Skidlz/PAiA-8700/Tape Programs/Micro-Drums/Micro Drums P1 & 2.pdf

# PracticalCircuitry

# MICRO DRUMS

# PARTI

# figure2 By: Tom Henry

Analog design has always fascinated me, and as a consequence I've never really gotten into digital or computer type circuits. However, just recently I dipped into this field and was amazed at the things that even a novice (like myself) can get a computer to do. As my first venture into this area, I came up with a computer controlled drum unit, called "Micro-Drums", which has absolutely revolutionized the manner in which I approach composition. Not being a drummer, my music has always been hampered by a lack of rhythmic expression, but this new circuit has changed all that.
What is Micro-Drums? Quite simply, it is a hardware/software combination which causes the PAIA 8700 microcomputer to think that it's a drummer. Up to eight drums can1 be polytonically controlled, over the range of an entire song. Nuances, bridges, breaks, lead-ins, even mistakes can be programmed into it so that the unit really drums as if it were a person. Depending on various factors, three to ten minute songs can be programmed with a great amount of depth and variation.
Editing a drum score is quite easy since an hierarchical approach is taken which closely approximates the manner in which you would write a song anyway. Once a score has been worked out, it can be saved to cassette and re-loaded at a later date. Thus, it is possible to create a library of drum scores and this eases the task of creating new songs later on.
But here's the real kicker. By using a special technique with the computer (the IRQ, to be discussed later), we can sync the drum unit to click tracks on tape, other rhythm generators, sequencers — or we can go the other way around! That is, Micro-Drums can be either a master or slave with equal ease. And best of all, this special technique drastically reduces both the hardware and software needed.
As mentioned, this project is based on the PAIA 8700 microcomputer. However, the same methods will work with just about any other computer using a member of the 6500 family, including the VIC-20,
Commodore 64, and PET. | As long as you can find one
32 | PUtyphuny | August 1983

uncommitted address and can get access to the IRQ pin of the CPU chip, you can make it work. By the way, if you do configure this around the 8700 you'll be glad to know that the new hardware in no way interferes with the rest of the computer. You can still use it for your other applications.
Like most computer projects, the basic principle is simple although the explanations get quite long-winded. To keep things orderly, this installment of "Practical Circuitry" details the hardware needed for Micro-Drums, while next time the necessary software and programming instructions are described.
Refer to the schematic in figure 1. Essentially, we set up one address in the 8700's operating system to act as a drum output port. This port is memory mapped, and each bit in it controls a sepa-
rate drum. | Writing a byte into this port triggers
the drums corresponding to the various bits. | Ad-
dress $0880 ("$" means that the number is in hexadecimal notation) is chosen for the drum output port, since this leaves the one at $0840 free for other synthesizer applications.
IC1 and IC2 are quad latches; their duty is to store the byte which is written to the drum port. Since a typical "write" operation on the data bus is only several microseconds long, we need these two chips to grab the desired byte and hold on to it. When a "write" occurs, the STROBE line of the 8700 goes low for a microsecond or two. This line goes to pin 5 of each of the latches, hence causing them to latch the bytes currently on the data bus.

# figure 1

NOTES

MICRO-DRUMS Computer Drum Interface Designer: Thomas Henry

All resistors in ohms.
All capacitors in mfd. except where noted.
All NOR gates =1/4 4001 | (IC4, ICS).
All inverters = 1/6 4049 | (IC6).
IC POWER CONNECTIONS:
4001 --- pin 7 = ground
pin 14 -- +5V
4049 -- | pin 1 | = +5V
pin 8 | = ground
Polyphony | August 1983 | 33

# PracticalCircuitry |

But the STROBE signal also goes to 103, which is a 555 timer set up as a one-shot. The output of this one-shot, upon being fired, goes high for a period of 1 millisecond. In effect, we have stretched out the STROBE signal (which is several microseconds long) to a 1 millisecond pulse. You will recognize this figure as being one of the standards we've talked about previously — it’s just the right length of time to fire envelope generators and drum circuits. In point of fact, every output in Micro-Drums generates a +5V, 1 millisecond wide pulse, and thus the circuit is compatible with any of the projects described in "Practical Circuitry".
By the way, notice how everything works out conveniently for the 555 input at pin 2. Normally, you have to provide some input conditioning to this pin, but as it turns out the STROBE signal from the 8700 has the correct polarity and pulse width so that all you have to do is just hook it up directly to pin 2. That ought to refute Murphy's Law!
Now backtrack just a bit to the latch outputs. Each output is buffered by a transistor (QI through Q8, one for each bit). Note that the transistor inverts the bit; however, the NOR gate following the transistor inverts the bit again. The net effect is that the bit passes to jacks JI through J8 exactly as it was written to the drum port. To put it another way, write the number $FF to the drum port and all of the drums will be fired; write a number $00 to the port, and none of them will be fired. Note that LEDs DI through D8 turn on according to the number written to the port. These provide an excellent indication of what's going on while you're composing a song.
So, the latched data is sent to the transistors and then to the NOR gates. Now one input of each NOR gate is tied to the stretched out STROBE signal (from IC3 and the inverter). This causes the selected NOR gate to go high for a period of 1 millisecond, and as mentioned above, this is just what envelope generators and drum circuits like to see. Notice that the stretched out STROBE signal is also available at J9. This signal may be used as a SYNC output and can lock sequencers, rhythm generators, and other computers to the main timing logic. Its pulse width is also 1 millisecond.
This takes care of the drum output support hardware. As you can tell, there really isn't very much to it, and in fact it is quite similar to the other output port at $0840 on the 8700. The rest of the circuitry in figure 1 has nothing to do with the drum output, but instead provides the necessary housekeeping circuitry to round out the complete system.
Let's look at the peripheral circuitry.___ Since we will be syncing the computer through its IRQ line (interrupt request), we must condition this input
somewhat. | J10 gives us access to this line. | Cl,
R20, and the inverter form a half-monostable and as such take an input pulse of variable length and transform it into a precise 10 microsecond trigger. This trigger couples to the computer via IRQ, found at J7 on the 8700.
Why should this be a 10 microsecond pulse? The answer to this lies in the nature of the IRQ line in general. When the IRQ line of the 6503 CPU is brought low, the computer will cease whatever it is doing and jump to the service routine pointed at by the vector in location $0FFE and $0FFF. Control is then sent to this service routine, and the instructions found there will be executed until an RTI (return) command is encountered. Control is then sent back to the main program.
Now suppose that the IRQ signal which caused all of this to happen is still low. (In other words, the execution time of the service routine was shorter than the pulse width of the IRQ signal.)
What will happen? | Just what you would expect; the
routine is called again! | The upshot is that one IRQ
signal caused the service routine to be called
twice. | We clearly don't need that, so the IRQ pulse
is shaved down to 10 microseconds. | With the 8700,
10 microseconds corresponds to about 5 program instructions, so as long as the service routine is more than 5 instructions long, all will work well. Incidentally, it should be clear that the IRQ pin responds to "levels", not "edges".
As you will see next time, when we discuss the software aspects of Micro-Drums, this IRQ business is the key to the entire system. Not only does it make master/slave relationships possible, but it also allows, use to achieve a remarkable analog to digital conversion for the price of a patch cord! And as mentioned before, both the hardware and software can be drastically simplified.
The remaining three inverters of the 4049 package are put to use as a variable clock. There's nothing clever here since this circuit has been around for years. But one interesting aspect is that C4, R19 and an inverter are set up as another
half-monostable. | This time the pulse width is made
to be millisecond wide (our old standard). | R23 sets
the clock rate, and with this control the output frequency can be continuously adjusted. Even though the frequency can be changed the pulse width will remain fixed at 1 millisecond.
Just to give you a sneak preview, a patch cord will be used to connect the CLOCK OUTPUT (Jll) to the SYNC INPUT (J10), and thus interrupts can be made to occur at an adjustable frequency. This method will be employed to set the tempo of the

This just about covers the hardware aspects of Micro-Drums, but perhaps a few words about construction methods should be said. I built this circuit on a prototype circuit board (from Radio Shack), using ordinary hookup wire. If you employ this method, be sure to ponder the layout so that you won't run out of room at a crucial moment! Watch your power supply connections, but since the circuit only uses a +5V supply, this shouldn't provide any great problem. Also (need I say it?), use sockets, since this project employs CMOS integrated circuits which can be damaged by static electricity. Figure two shows the complete parts list for Micro-Drums. After constructing the circuit, give a great deal of thought on how you will interface it with the computer. I used ribbon cable and headers to complete the connections to JI and J7 on the 8700. After making the connections I mounted the board to the back of the 8700 computer itself. If you already have this computer, then you will know that it is a double-decked circuit board arrangement. By adding the Micro-Drums card, you will be left with a triple-decked affair.
And now is as good a time as any to mention a modification to the 8700 that you really ought to
34 | Polyphony | August 1983

PracticalCircuitry........

think about. I found that with just the dare-bones computer (no Micro-Drums added on), the power supply ran extremely hot. I took some measurements and discovered that the unit was drawing almost 900 mA! This is clearly way too much for the 7805 regulator to handle with such a small heatsink. The culprit, of course, is the RAM — each chip consumes almost
70 mA. | Multiply that by 8 (the number of 2112s in
the 8700), | and you've got quite a load for the
regulator to handle.
In general I like to have at least a 2:1 margin of safety, so I decided to modify the computer
accordingly. | I simply built another +5V power sup-
ply and put the RAM on their own circuit. | It's a
crazy scheme, I know, but it does work and both power supplies now run considerably cooler. What's more, in the future I will be able to add on extra circuitry since I have a little more juice to play with now.
If what I've said doesn't make any sense to you, then don't perform the modification!!! Your 8700 is a valuable instrument and you won't want to wreck it. On the other hand, if you understand about power supplies, decoupling, and computers — and if you have a steady hand for cutting PC board traces — you might want to give this a try. Remember, the RAMs must be completely on their own circuit; it's no good just wiring two power supplies in parallel (unless you get off on rampant destruction of valuable equipment and enjoy fireworks).
After building the Micro-Drums card and performing the modification (if this applies to you), you can then put the thing in a suitable house,
figure 2 shows how I did it. | This is a home-
made wooden box with two sheets of steel for a top and bottom. The 8700 is bolted to the top panel, and the keyboard shines through a square hole cut in
the metal. | I put some foam rubber around the hole
and this keeps dust and moisture out. | By the way,
the fuse, switch, and line cord are on their own small panel mounted on the back surface of the box. If you are using the PAIA 8700 power supply, then bring out the 60 Hz signal output to a front
panel jack as well. | (This is a logic level signal,
NOT the line voltage!!!) | Since this is a reliable
frequency source, it might come in handy for future

As you examine the photo fig. 2 you will probably notice some features not described in the article
(knobs, connectors, etc.). | These have nothing to do
with the Micro-Drums interface. | For example, there
are two D-25 jacks on the right side; one of these is a dummy (for future expansion) and the other is an interface to my keyboard synthesizer. When you build your unit, you might like to plan for the future, too, and leave some extra room for more '.onnectors and whatnot.
Well, that wraps up the Micro-Drums hardware and it's a good thing too, since we're out of space. But come back next time for the concluding episode and see how to implement the software for a complete
drum computer. | Until then, here's a challenge for
you to ponder: | how would you create a real time
clock using the SYNC input, the 60 Hz output, a patch cord, and a bit of software?

re-view continued from page 9

front-to-rear as well as left-toright. This 3-dimensiona1ity makes his heavily-produced electronic pop tunes a listening experience which goes beyond their significance as pop tunes. Other influences might be Zappa and Godley/Creme.

Berlin | Pleasure Victim | (Geffen
2036). | I didn't want to like this
group — their music is too trendy and their videos have been a little pretentious. But after having played the record numerous times looking for a weakness to attack, I have to admit it grew on me; Terri Nunn's voice has a cloying innocence and John Crawford's and David Diamond's synthi backing is very professional. It's well defended from sharks like me.
Men at Work | Business as Usual
(Columbia FC37978); Cargo | (Colum-
bia QC38660). | MAW has been called
"the Velveeta of pop". | However,
it's | precisely because | their
strong, well-crafted tunes appeal to even a jaded old reviewer that they're selling so many records. Despite the cheese.
Deckard/Cardwell/Vosh | Sound
(cassette). | "Sound" is what it's
all about, | as this synthesizer
trio spins long, | introspective
pieces full of original synthesizer sounds. Sounds that soothe, sounds that startle, sounds that bounce off the wall and refuse to leave -- always the devotion for The Sound. $4 postpaid from David Vosh, 6300 Goldenrod Court, Upper
Marlboro, MD | 20772.
Everfriend | Key Essentials | (cas-
sette). | Keyboard artist Bill
Rhodes displays his skills, from Keith Emerson-like classical rock to piano fusion jazz to the dramatic' "I,ife and Death of a Star" (reviewed May/June '81 as an EP). There's a couple vocal numbers too — too bad the vocalist he chose sounds a little tentative. Never mind; the rest is top drawer. Contact Bill at 1 Windemere Rd., Piscataway, NJ 08854.
continued on page 44

The new Series V Digital/Analog Keyboard Controllers from PAIA offer enough standard features and options tofill every need
| from stage to studio. | Standard features
include Pitch & Modulation Wheels, Gate and Re-trigger outputs, Low Note Rule Priority, Smooth Pratt-Read Action, Light
| weight and only 2" high.
| You have your choice of:
| • 37 or 61 Note Actions • Exponential Or Linear C.V. • MIDI or Parallel Digital • Mono or Poly • Factory Assm. or Low Cost Kits

Best of all, prices start at less than $180

## call ourtoll-freeline

1-800-654-8657

| 9AM to 5PM CST MON FRI

## for price& ordering details & get yourfree RAiA catalog!

Direct mailorders and inquiries to. Dept.11y
miAElectronics, Inc.

.1020 W Wilshire . Oklahoma City. OK 73116 (405)843 9626 J

i-oiyphony | August 1983 | 35

# PracticalCircuitry

# MICRO □RUMS

# PART II

# By: Tom Henry

Last time in "Practical Circuitry" we discussed the hardware needed to implement Micro-Drums, a computer controlled drum unit. In this installment we will consider the software side of things. Since a lot needs to be said, let's jump right in and see how to punch up the program required to get Micro-Drums off and drumming!

Entering the program. Figure 1 shows the complete listing for Micro-Drums software. Since I used the PAIA 8700 computer, the code is written in 6502 assembly language. Those of you who plan to use Micro-Drums with some computer other than the PAIA unit will need to change the appropriate equates (at the start of the program) and may also need to alter the starting address. The source code in Figure 1 is heavily annotated, so you should be able to figure out how it works quite easily.
8700 users can ignore the
line numbers, labels, mnemonics and comments if desired, since all that is needed to enter the program is the start address and the required code (under the heading "CODE", in the listing). Refer to your 8700 Computer/Controller manual for help in deciphering an assembler listing if you experience any difficulty.
Follow these steps to enter the program:
(1) Turn on the computer and hit the reset button.
(2) Load location $ED with the byte $1F. This sets the stack to a known condition needed by

Micro-Drums.

(3) Get ready to start loading data at $0120, by punching in this address and hitting the DISP
(4) Using Figure | 1 | as | a
guide, start entering the data. The first few bytes are $20, $34, $0F, A5, etc.
(5) Keep entering data until you hit the last byte in the list-
ing. | This is $02 (at location
$0288). | Use the PCH and PCL keys
to confirm that you're at the right place.
(6) You're now ready to save the program to tape. Follow the normal 8700 Cassette Interface protocol for saving a program. The start address in $1020, the end address is $0288, and you can use $01 for an identifier.

If all has gone well, you now have a working copy of the Micro-Drums program. After debugging your work (if needed), make a few backup copies as well. Now, let's see how to use the complete Micro-Drums system.

Using Micro-Drums. To use
Micro-Drums, follow these instructions:
(1) Reset the 8700 computer.
(2) Load location $ED with the byte $1F. This sets the stack to a known condition needed by Micro-Drums. Do not forget this step; the program will not load or run correctly if it is left out!
(3) Using the standard load-
ing procedure, | load the Micro-
Drums software. | The start address
is $0120, the end address is $0288 and the identifier is $01.
(4) Run the program by typing $025F and hitting the RUN key. If everything has gone well, you will hear a long beep. This long beep indicates that you are in the main loop, and the computer is awaiting your instructions.

When in the main loop (as you now are), you have a choice of four commands. They are COARSE EDIT, FINE EDIT, TAPE and PLAY. After any of these commands have been executed, you will always be ushered back to the main loop. Even though the 8700 has limited display capabilities, you can always tell when you are back in the main loop by the long beep. Also, if you hit an invalid key when in the main loop, a long beep will occur. By listening for this beep, you can always tell what's happening at any moment.
Here follows a description of the four main commands. Note that when within the four main commands, there are other minor subcommands possible.

FIKE EDIT. The fine edit
command defines measures of patterns which will be used as the basis for the entire song. You may define up to eight different patterns, each one up to 32 beats long. Or you may partition this in other ways; for example, four patterns of 64 beats each.
Each pattern is given a num-
ber-name. | The numbers 0 through 7
18 | Polyphony | October 1983

are used for this purpose. To start editing a given pattern, when in the main loop type the number-name and then hit the PCL key. (Mnemonic: think of PCL as "low", for lowest level of edit-
ing, | the pattern.) | So to start
editing pattern zero, type $00 and then hit the PCL key.
You will now be sent from the main loop to the FINE EDIT routine. The display will show the current beat number, and the drum LEDs will show the drums to be played during that beat. To turn a drum on for the beat, touch one of the keys from 0 to 7. The corresponding LED will light up, and all of the currently selected drums will be played as a test. You can turn a drum off by touching the corresponding drum key again. Thus, the drum keys are like toggle switches and may be used to turn drums either on or
off. | There is one limitation,
though: | you may not have a parti-
cular beat play all eight drums at once. You can have up to seven drums playing at once, but not all of them. (The software uses the all-eight condition as an end-ofthe-pattern marker.)
When you have achieved the selection of drums desired, touch the ENTER key. This will store the selection, then increment the beat pointer. The display will show the next beat number, and you are all set to enter the next selection. Also, when the display increments, the drums currently selected for the new beat will be triggered once. Thus you can single step through a pattern, for trial purposes, just by touching the ENTER key repeatedly. You can back step with the BACK key just as easily. And if you want to hear the current beat several times, touch the DISP key. This will sound the current drum selec-
| As mentioned, | keys 0 to 7
stand for drums 0 to 7. | Key 8
stands for a rest. | This clears
out the drums selected for that beat. When you are done editing a pattern, touch the 9 key and you will be ushered back to the main loop. Note that even though the pattern may be up to 32 beats long, you are not obligated to use all of the beats. For example, with 5/4 time you might want to only use 10 beats.
| COARSE EDIT. | After creating
some patterns (see above), | you

OOOO1
00002
00003
00004
00005
00006
00007
00008
00009
OOOIO

00012
00013
00014
00015
00016
00017
00018
00019
00020
00021
00022
00023
00024
00025
00026
00027
00028
00029
00030
00031
00032
00033
00034
00036
00037
00038

OOOO
OOOO
OOOO
OOOO
OOOO
OOOO
OOOO
OOOO
OOOO
OOOO

OOOO

OOOO
OOOO
OOOO
OOOO
OOOO

OOOO
0120
0120 20 34 OF

?*<*<«»*•**«»*»***«»*•*«*****«•*********
S» | | | *
J* | MI8RO-DRUMS | *
;* | MICROCOMPUTER CONTROLLED DRUM UNIT | *
;* | | | *
S* | (8) 1983 | THOMAS HEl'tfiY | *
5* | VERSION 2.1 | FEBRUARY 5, 1983 | *

I
s
IROVES --- *OO | ; IRQ VE8T0R.
PATTER --- «O3 | J PATTERN POINTER BASE.
SELE8T = 405 | ;DRUM SELE8T BIT PATTERNS.
PARAMS --- *OD | J TAPE PARAMETERS.
BEAT | = *14 | ;CURRENT BEAT POINTER.
SPOINT -- 415 | 5CURRENT EVENT SELECTED.
REPEAT -- *16 | ; CURRENT REPEAT COUNTER.
BUFFER -- *FO | J KEYBOARD BUFFER.
SCORE | = *0280 | ;DRUM SCORE AREA.
DISPLA --- *0820 | i DISPLAY ADDRESS.
DRUMS | --- *0880 | J DRUM OUTPUT ADDRESS.
RELAYS -- *OE25 | 5 TURN ON TAPE RELAYS.
CASS | = «0EAA | ;PERFORM CASSETTE OPERATION.
DECODE -- *OFOO | 5 INPUT A BYTE.
SETKEY -- *OF1F | JGET A BYTE.
BEEP | -- *OF22 | ; BEEP THE BEEPER.
LBEEP | = *OF24 | JWITH SETUP, GIVES LONG BEEP.
SHIFT | -- *OF34 | JSHIFT BUFFER BY ONE DIGIT,

s
J»»* MAIN LOOP ***

* = *0120
S
NUMBER JSR SHIFT | JSHIFT IN NEW DIGIT.
00039 | 0123 | AS FO | | LDA BUFFER | 5FETCH PACKED ENTRY.
00040 | 0125 | 8V 20 08 | | STA DISPLA | J THEN UPDATE THE DISPLAY.
00041 | 0128 | 4C 31 01 | | JMP INPUT | ;go get next input.
00042 | 0128 | A2 FF | MAIN | LDX #*FF | SGET READY FOR LONG BEEP.
00043
00044 | O12D | 18
| O12E | 20 24 OF | | CLC
| | | | JSR LBEEP | 5 DO LONG BEEP.
00045 | 0131 | 20 IF OF | INPUT | JSR GETKEY | ;WAIT FOR KEYSTROKE.
00046 | 0134 | C9 IO | | CMP #*10 | J IS IT A NUMBER?
00047 | 0136 | 90 E8 | | BCC NUMBER | J YES, BRANCH BACK AND GET
00048 | 0138* C9 10 | FIND | CMP #«1O | JIS IT 'PLAY'?
00049
00050 | O13A | FO OF
0138 C9 14
| | | | BEQ PCMD
| | | | CMP #*14 | $IS IT ’COARSE’?
00051
00052 | O13E | FO 52
0140 C9 15
| | | | BEQ COARSE
| | | | CMP #*15 | ;IS IT 'FINE'?
00053
00054

0142 FO OA
0144 C9 16
| | | | BEQ FINE
| | | | CMP #*16 | JIS IT 'TAPE'?
00055 | 0146 | DO E3 | | BNE MAIN | 5RAN OUT OF COMMANDS.
00056 | 0148 | 4C 37 02 | | JMP TAPE
00057 | 0148 | 4C E3 O1 | PCMD | JMP PLAY
00058
00059
00060
00061
00062
00063 | 014E
| 014E
| 014E
| O14E
| 014E | A5 FO | r
;»*» FINE EDIT COMMAND *»•
| | | S
| | | FINE | LDA BUFFER | J GET PATTERN NUMBER.
00064 | 0150 | 20 57 02 | | JSR OFFSET | J GET PATTERN OFFSET.
00065 | 0153 | AO 00 | | LDY #*OO | J ZERO OUT THE BEAT POINTER.
00966
00067
00068

0155 C8
0156 88
0157 8C 20 08

SHOWIT INY
BACKUP DEY
| | | | STY DISPLA | J DISPLAY IT.
00069 | O15A | Bl 03 | | LDA (PATTER),Y | »GET SELECTED BEAT,
00070 | 0158 | 8D 80 08 | | STA DRUMS | J AND PLAY IT.
00071 | 015F | 20 4F 02 | FEDIT | JSR FETCH | J GET EDIT KEYSTROKE.
00072 | 0162 | 89 12 | | CMP #*12 | SIS IT A ’BACK’?
00073 | 0164 | FO FO | | BEQ BACKUP | 5YES, BACKSPACE ONCE.
00074 | 0166 | 89 11 | | CMP #*11 | SIS IT A ’DISP’?
00075 | 0168 | FO EB | | BEQ SHOWIT | SYES, PLAY CURRENT BEAT.
00076 | 016A | 89 OA | | CMP #*OA | SIS IT A DRUM NUMBER (0-9)?
00077 | 0168 | 90 08 | | BCC DENTER | SYES, GO ENTER DRUM BEAT.
00078 | 016E | 89 13 | | CMP #*13 | SIS IT AN 'ENTER'?
00079 | 0170 | DO ED | | BNE FEDIT | SNO, RAN OUT OF COMMANDS.
00080
00081

0172 88
0173 48 55 O1
| | | | INY | SYES, ADVANCE TO NEXT BEAT.
| | | | JMP SHOWIT
00082 | 0176 | 89 09 | DENTER CMP #*09 | S#*09 MEANS END OF PATTERN.
00083
00084

0178 DO 06
| O17A | A9 FF | | BNE NEXT1
| | | | LDA #*FF | SEND OF PATTERN MARKER.
00085
00086

0178 91 03

| 017E | DO AB | | STA (PATTER),Y
| | | | BNE MAIN | 5 BRANCH ALWAYS.
00087 | 0180 | 89 08 | NEXT1 | CMP #*08 | J#*08 MEANS ’REST’
00088
00089
00090

0182 DO 04
0184 A9 00
0186 FO 05
| | | | BNE NEXT2
| | | | LDA #*0O
| | | | BEQ STORE | 5 BRANCH ALWAYS.
00091
00092

0188 AA
0189 B5 05
| | | NEXT2 | TAX | ;INDEX INTO BIT PATTERN.
| | | | LDA SELECT,X | SGET PROPER BIT PATTERN.
00093 | O18B | 51 03 | | EOR (PATTER),Y | 5 ADD IN NEW BEAT.
00094 | O18D | 91 03 | STORE | STA (PATTER),Y | SAND SAVE IT.
00095 | O18F | 48 55 O1 | | JMP SHOWIT | ;SOUND THE DRUM BEAT.
Pobphony | October 1983 | 19

00096 0192
00097 0192
00090 0192
00099 0192
OOIOO | 0192
OO101 | 0192 | A6 FO
00102 | 0194 | 86 15
00103 | 0196 | A6 15
00104 | 0198 | BD 80 02
00105 | 0198 | 85 FO
00106 | O19D | SO 20 08
00107 | 01 AO | 20 IF OF
00108 | O1A3 | C9 IO
00109 | O1A5 | 80 08
001 IO | 01A7 | 20 34 OF
OO111 | O1AA | A5 FO
OO112 | O1 AC | 4C 9D 01
OOl 13 | 01AF | C9 13
OO114 | 0181 | DO OC
OOl 15 | 0183 | A6 15
OOl 16 | 0185 | A5 FO
OOl 17 | 0187 | 90 80 02
OO 118 | O1BA | 15
00119 | O1BC | 4C 96 O1
00120 | O1BF | C9 12
00121 | O1C1 | DO 05
00122 | 01C3 | C6 15
00123 | 01C5 | 4C 96 01
00124 | O1C8 | C9 14
00125 | 01CA | DO 05
00126 | 01CC | A5 15
00127 | O1CE | 4C 9D O1
OOl 28 | O1D1 | C9 11
00129 | O1D3 | FO Cl
00130 | 01 D5 | C9 17
00131 | O1D7 | DO C7
OOl 32 | O1D9 | A6 15
00133 | O1DB | A9 OO
OO 134 | O1DD | 9D 80 02
00135 | OiEO | 4C 28 O1
00136 01E3
00137 O1E3
00138 O1E3
OOl 39 O1E3
00140 O1E3
00141 | 01E3 | A9 00
00142 | 01E5 | 85 16
00143 | 01E7 | A9 FF
00144 | O1E9 | 85 15
00145 | O1EB | 58
00146 | 01EC | C9 FF
OO147 | OlEE | FO FC
00140 | O1FO | 4C 28 01
00149 01F3
00150 01F3
00151 | O1F3 | 20 OO OF
00152 | 01F6 | C9 OO
00153 | 01F8 | DO 04
00154 | 01FA | 28
00155 | O1FB | 78
00156 | O1FC | 08
00157 | O1FD | 40
00158 O1FE
00159 O1FE
00160 | 01FE | A5 16
00161 | 0200 | DO 19
00162 | 0202 | E6 15
00163 | 0204 | A6 15
00164 | 0206 | BD 80 02
00165 | 0209 | FO EF
00166 | 0208 | 85 16
OO167 | O20D | E6 15
00168 | 02OF | A6 15
00169 | 0211 | BD 80 02
00170 | 0214 | 20 57 02
00171 | 0217 | A9 OO
00172 | 0219 | 85 14
OOl73 | 0218 | A4 14
00174 | 021D | Bl 03
00175 | O21F | C9 FF
00176 | 0221 | DO 08
00177 | 0223 | C6 16
00178 | 0225 | A9 00
00179 | 0227 | 85 14
00180 | 0229 | FO C8
00181 | 0228 | 8D 80 08
00182 | O22E | 8C 20 08
00183 | 0231 | E6 14
00184 | 0233 | A9 FF
00185 | 0235 | DO
00186 0237
00187 0237
00180 0237
00189 0237

1
J*»* COARSE EDIT COMMAND ***
COARSE LDX BUFFER | J GET DESIRED EVENT NUMBER.
| STX SPOINT | S STORE AT CURRENT EVENT.
REVEAL LDX SPOINT
| LDA SCORE,X | J GET CONTENTS OF EVENT.
| STA BUFFER | JPUT IN BUFFER AND
VIEW | STA DISPLA | JSHOW IT TOO.
LOOP | JSR SETKEY | 5 GET KEYSTROKE.
| CMP #♦10 | J CHECK FOR NUMBER.
| BCS NONUM | J NOT A NUMBER, BRANCH.
| JSR SHIFT | JSHIFT IN NEW DIGIT.
| LDA BUFFER | ;FETCH PACKED ENTRY.
| JMP VIEW | J AND UPDATE DISPLAY.
NONUM | CMP #$13 | ;IS IT AN ’ENTER’?
| BNE NEXT3 | J NO, GO ON.
| LDX SPOINT | J RE-GET EVENT NUMBER.
| LDA BUFFER | ;FETCH INPUT NUMBER.
| STA SCORE,X | 5 STORE IN SCORE.
| INC SPOINT | ;UPDATE EVENT NUMBER.
| JMP REVEAL | JUPDATE DISPLAY.
NEXT3 | CMP G$ 1? | JIS IT A BACKSPACE?
| BNE NEXT4 | J NO, BRANCH ON.
| DEC SPOINT | 5DECREMENT EVENT COUNTER.
| JMP REVEAL | ;SHOW CONTENTS OF EVENT.
NEXT4 | CMP #♦14 | J IS IT A ’PCH’?
| BNE NEXT5 | ;NO, BRANCH ON.
| LDA SPOINT | 1 GET CURRENT EVENT NUMBER.
| JMP VIEW | ;AND SHOW IT.
X T5 | CMP #♦11 | JIS IT A ’DISP’?
| BEQ REVEAL | J IF SO, SHOW CONTENTS.
| CMP #♦17 | J’REL’ STANDS FOR ALL DONE.
| BNE LOOP | J RAN OUT OF COMMANDS.
| LDX SPOINT | J RE-GET EVENT NUMBER.
| LDA #♦00 | J END OF SCORE MARKER.
| STA SCORE,X
j | JMP MAIN | J RETURN TO MAIN LOOP.

’LAY’ COMMAND ENTRY ***

play | LDA #♦00 | J ZERO OUT REPEAT AND
| STA REPEAT | J SCORE POINTER.
| LDA •♦FF
| STA SPOINT
| CLI | JPREPARE FOR IRQ.
TISHT | CMP •♦FF | J•♦FF MEANS KEEP PLAYING.
| BEQ TIGHT | J STAY IN TIGHT LOOP.
| JMP MAIN | J ABORT ’PLAY’ NOW.
IRQRTN JSR DECODE | J SEE IF ZERO KEY IS PUSHED.
CMP •♦OO
BNE PLAMOR | J IT ISN’T, SO PLAY MORE.
FINISH PLP | J SET INTERRUPT FLAG
SEI | J SO NO MORE OCCUR.
PHP
RETURN RTI
PLAMOR LDA REPEAT | JREPEATED OLD PATTERN ENOUGH?
BNE MORE | J NO, KEEP GOING WITH OLD ONE.
INC SPOINT | J YES, UPDATE SCORE POINTER.
LDX SPOINT
LDA SCORE,X | J GET REPEAT TIME DATA.
BEQ FINISH | J DONE PLAYING WHOLE SCORE.
STA REPEAT | J CONTAINS NUMBER OF REPEATS.
INC SPOINT | J UPDATE SCORE POINTER.
LDX SPOINT
LDA SCORE,X | J GET PATTERN NAME DATA.
JSR OFFSET | J GET PATTERN ADDRESS OFFSET.
LDA •♦OO
STA BEAT | J ZERO OUT BEAT POINTER.
MORE | LDY BEAT | JY INDEXES TO PROPER BEAT.
LDA (PATTER),Y | JGET OUTPUT DATA.
CMP •♦FF | J END OF PATTERN?
BNE OKAY | J NO, GO PLAY THE BEAT.
DEC REPEAT | J DECREMENT REPEAT TIME.
LDA #♦00 | JYES, RESET BEAT COUNTER.
STA BEAT | J THEN TRY AGAIN.
BEQ IRQRTN | (BRANCH ALWAYS.
OKAY | STA DRUMS
STY DISPLA
I | BEAT | J UPDATE BEAT POINTER.
LDA •♦FF
BNE RETURN | J BRANCH ALWAYS.

; *»* ’LOAD’ AND ’SAVE’ COMMAND *** will then string them together in various arrangements to form the
complete song. | This is COARSE
editing. | You will create a score
by entering some events; | each
event consists of two entries. The first entry is the number of times you wish a pattern to repeat , and the second entry is the number-name of the pattern which
is to be repeated. | There is room
for 64 events total. | This will
allow songs up to fifteen minutes long to be programmed! To g»t into the COARSE EDIT mode from the main loop, type the number of the event you wish to start at (usually a $00) and then the PCH key. (Mnemonic: think of PCH as "high", the highest level of editing.) The display will now show the contents of the current event. To enter a new event, type the desired number and hit the ENTER key. The event will be recorded, and the score pointer is incremented once. For example, starting at event zero, to get sixteen repeats of one, type $10, ENTER, $01, ENTER. Note that all numbers are in hexadecimal and that each entry must be followed by an EN-TER.
You can backspace through a score with the BACK key. Also, to see the current event number, touch the PCH key at any time. To see the contents of the event, type DISP. Using the keys just mentioned, you can step through an entire score in a matter of minutes and change or update it as needed.
To finish off a score, touch the REL key. This puts in an end of score marker and returns you to the main loop. A long beep will occur.
PLAY. | Playing a score is
easy. | First make sure that the
SYNC INPUT jack has some source of triggers. You may sync the drum score off of the internal variable clock, an external clock, keyboard triggers, sequencer triggers, or click tracks from a tape deck. The input pulses should be +5V in magnitude. Note that Micro-Drums' internal variable clock meets this need and is perhaps the easiest to
use. | In addition it allows easy
adjustment of the tempo: | just
dial in the desired speed. | This
may not seem like much, but consider what we've just done: a potentiometer controls the tempo, continuously, without the intervention of an analog to digital con-
20 | PObliiony | October 1983

verter. How's that for saving money and keeping things simple! After providing some source of sync pulses, you may start playing the score simply by touching the RUN key. When the song is finished, you will be sent back to the main loop and a long beep will occur. You can also abort a song while it is playing by touching the 0 key. Once again, you will return to the main loop.
As you can see, the SYNC
INPUT (alias the IRQ) is the key to the power of Micro-Drums. Any circuit which can put out a series of pulses can cause Micro-Drums to step through the song, beat after beat. You are not constrained to meet this or that condition, and the circuitry is perfectly general. Simply send the computer some pulses and the song commen-
ces! | And don't forget the SYNC
OUTPUT jack either. | You can cause
some other circuit (like a sequencer) to follow Micro-Drums just as easily, so Micro-Drums can thus play the role of master or slave with equal ease.
TAPE. | You can save or load
scores using this command. | To
save a score, start the recorder going in the record mode, type $DD and touch the TAPE key. The computer will do the rest; there is no need to enter any addresses,

Loading a score is just as easy. Start the recorder going in the play mode, type $11 and hit the TAPE key. The score will be loaded.
At the end of any tape operation you will be sent back to the main loop, and a long beep will indicate this fact. Note that the load and save options affect the entire score and pattern memory, so don't be alarmed if the operation takes up to a minute or so. If you experience any trouble, refer to the 8700 Cassette Interface manual and review how to set volume levels and so on.

The future. Well, that just about wraps up how to use Micro-Drums. Of course, all we have done here is talk about the mechanics of using the unit; it's up to you to think about the musical side of things. For example, if you know that a particular pattern is to contain both eighth notes and triplets, then you will need to divide the pattern into groups
of | twenty-four | (three | times
00190 | 0237 | | ;
OO191 | 0237 | A2 07 | TAPE | LDX #*07 | PREPARE TAPE PARAMETERS.
00192 | 0239 | 85 OC | SETFIL LDA PARAMS-1,X | ;GET PARAMETERS.
00193 | 0238 | 95 FO | | STA BUFFER,X | 5 AND STUFF IN PLACE.
00194 | 023D | CA | | DEX
00195 | O23E | DO F9 | | BNE SETFIL | ;KEEP STUFFING IF NEEDED.
00196 | 0240 | A5 FO | | LDA BUFFER | J GET LOAD/SAVE TOKEN.
00197 | 0242 | 20 25 OE | | JSR RELAYS | ;TURN ON RELAYS.
00198 | 0245 | 20 AA OE | | JSR CASS | ;PERFORM LOAD OR SAVE.
00199 | 0248 | 18 | | CLC
00200 | 0249 | 20 22 OF | | JSR BEEP | ;TURN OFF RELAYS AND BEEP.
00201 | 024C | 4C 2B O1 | | JMP MAIN | ;ALL DONE!
00202 | 024F | | 5
00203 | 024F | | ;
00204 | 024F | 84 14 | FETCH | STY BEAT | j GET A KEY, BUT SAVE
00205 | 0251 | 20 IF OF | | JSR GETKEY | ;CURRENT Y—REGISTER.
00206 | 0254 | A4 14 | | LDY BEAT
00207 | 0256 | 60 | | RTS
00208 | 0257 | | ;
00209 | 0257 | | ;
00210 | 0257 | OA | OFFSET ASL A | 5 FIND OFFSET BY
00211 | 0258 | OA | | ASL A | ;MULT IPLYING ACCUMULATOR
00212 | 0259 | OA | | ASL A | i BY SIXTEEN.
00213 | 025A | OA | | ASL A
00214 | 0258 | OA | | ASL A
00215 | 025C | 85 03 | | STA PATTER | iOFFSET ADDRESS IS HERE.
00216 | 025E | 60 | | RTS
00217 | O25F | | ;
00218 | 025F | | ;
00219 | O25F | ;*** INITIALIZATION ROUTINE **♦
00220 | O25F | | ;
00221 | O25F | | ;
00222 | O25F | 78 | | SEI
00223 | 0260 | A2 OO | | LDX #«OO
00224 | 0262 | BD 78 02 | MOVE | LDA DATA,X | ; GET DATA BYTE.
00225 | 0265 | 95 OO | | STA IRQVEC,X | 5STUFF IT INTO O-PAGE.
00226 | 0267 | E8 | | INX
00227 | 0268 | EO 14 | | CPX #*14 | ?NUMBER OF BYTES+1.
00228 | O26A | DO F6 | | BNE MOVE
00229 | O26C | AO OO | | LDY #*00 | 5CLEAR PATTERN AREA.
00230 | 026E | A9 OO | | LDA #*OO
00231 | 0270 | 91 03 | CLEAR | STA <PATTER),Y | ,
00232 | 0272 | 88 | | DEY
00233 | 0273 | DO FB | | BNE CLEAR
00234 | 0275 | 4C 28 O1 | | JMP MAIN | ,GO START UP MICRO-DRUMS.
00235 | 0278 | | ;
00236 | 0278 | | ;
00237 | 0278 | ?*»* DATA AND ADDRESS TABLES ***
00238 | 0278 | | ;
00239 | 0278 | | 5
00240 | 0278 | 4C | DATA | .BYTE *4C | ;OPCODE FOR ’JMP’.
00241 | 0279 | F3 O1 | | .WORD IRQRTN | ;START OF IRQ ROUTINE.
00242 | 027B | OO 03 | | .WORD *0300 | ;PATTERN BASE ADDRESS.
00243 | 027D | O1 | | .BYTE *01, *02 | ;DRUM SELECT BIT PATTERNS.
00243 | O27E | 02
00244 | 027F | 04 | | .BYTE *04, *08
00244 | 0280 | 08
00245 | 0281 | 10 | | .BYTE *1O, *20
00245 | 0282 | 20
00246 | 0283 | 40 | | .BYTE *40, *80
00246 | 0284 | 80
00247 | 0285 | OO | | .BYTE *OO | ;FILE PARAMETER.
00248 | 0286 | FF 03 | | .WORD *O3FF | ;TAPE END ADDRESS.
00249 | 0288 | 80 02 | | .WORD *0280 | ?TAPE START ADDRESS.
00250 | O28A | 80 02 | | .WORD *0280 | iTAPE POINTER.
00251 | 02BC | | | . END

ERRORS -- ooooo

END OF ASSEMBLY

eight). This is just one example of one of the musical considera-
tions | that must be taken into
account with Micro-Drums. | How-
ever, you will find that the more you play with Micro-Drums, the better you will become at visualizing what needs to be done.
Well, we've run out of room and need to start planning other projects. But in the meanwhile, as you play with the unit, think about how you would implement sequencer interfaces with Micro-Drums. The procedure is actually quite simple due to the "magical" way in which the SYNC INPUT works. Then consider synchro-sonic re-
cording; | how would you do this
with Micro-Drums? | Once again, the
basic principle is quite simple. Think about these things and perhaps later on in the pages of "Practical Circuitry" we can com-
pare notes. | __________________ _
Polyphony | October 1983 | 21
