Skidlz/PAiA-8700/Tape Programs/Poly-Split/Poly-Split.pdf

# POLY-SPLIT

Many times we've talked about how the personality of our computer based equipment is a function of the Operating system software that we happen to be running at the moment. Let's play some head games with the gear and feed it some code that will give it a split personality.
POLY-SPLIT does just that; it gives us two complete polyphonic synthesizer systems under the control of one keyboard. Play a chord or note on the lower keys and they are always assigned to a lower group of outputs. Play on higher keys and the result is assigned to another group.
Before we get into the listing of this program and its operation and use, we need to keep one fact clearly in mind;
POLY-SPLIT is simply an | extension | of | the | polyphonic
personality offered in MUS 1.0. All of the options offered by that code (STGs, dynamic output refresh, etc.) are provided by this one also. Since many of MUS l.O's subroutines are used by
POLY-SPLIT you must have this PROM or | its | equivalent
available, and the variables that you manually initialize for MUS 1.0 (see LAB NOTES: MUS 1.0, April/ May 1978 Polyphony) must be set for POLY-SPLIT also.
In addition to OUTS, CTRL, etc. which MUS 1.0 used there is a new variable which is unique to POLY-SPLIT; OUT2 ($BF). This is the variable that tells the program how many channels are to be set aside for use exclusively by AGO keys below the split point. Notice specifically that if MUS l.O's STG option is selected, the number entered into this variable must include those channels which will be producing envelope transients, (i.e. The number entered for OUT2 will always be an even number when STGs are being used.)
For example, if you have hardware (QuASH, etc,) for eight channels, this number is entered into the normal MUS 1.0 location for it; OUTS ($EA). If you want to split these into· three channels for low keys and five for high keys, you would set OUT2 ($BF) to contain 03.
The program appears at the end of this column and is loaded starting at location $000 in the same way that we've loaded programs in the past. If you're the careful sort, you will also save the program on tape as soon as it's loaded so that if there's a problem it won't wipe out all of your work. When the program has been loaded, preset the MUS 1.0 variables according to your preferences and application, and set the low channels variable (OUT2) as discussed above.
Run the program from location $000. With POLY-SPLIT running, keys 0 and 1 on the command keyboard retain the functions that they had under MUS 1.0. Key 0 clears and mutes the system; key 1 causes all of the channels to produce a note corresponding to middle C on the AGO keyboard.
A use for command key 2 has now been added; it provides a means of changing the split point while you're playing. Touch this pad and, as long as it's held down, any key on the AGO keyboard that you press will become the new split point. Now while playing, any key below the split point will be assigned to the channels that you've set aside for them, while keys greater or equal to the split point will be assigned to the remaining channels.

10011-
1002-
1004-
1006-
1008-
1011A-101l8-
100D-1010-
1013-
1016-
1018-
101A-101C-101E-1021-
1023-
1025-
1027-
1029-
1026-
102()-

0020

0010 :-·---

0030
8049
0050
0060
0070
0080
0090
0100 :•
:• | • :• | POLY-SPLIT | * :• | • :• A PROGRM FOR POL YPHCllIC •
:• | SPLIT KEY800IID | • :• | • :• | BY
:• | JO!tl Sil'IOOTOO | •

0110 : • <C> 1979 - PAIA ELECTROOICS * 0120 :•
0130 : ************ 1 1 1 1 1 1 1 1 1 1 • •********

0010 KTBI. • OL 00E0
0028 NTBL . OL 0008
0030 HKEY . Dl 00A2
0040 SPl T . Dl 00111
0050 ruT2 . OL 00EC
0860 oun . DL 00EB
0070 MS . Dl 00EA
0080 TRr.N . Dl OOC3
0090 !NI T . Dl 0021
0100 NOTE . Dl 0028
0110 POLY . Dl 0071
0128 DECO . OL 0F00
0130
0140 :FIRST, SYSTEM THINGS ARE DISPOSED OF. TIE SYSTEl1 IS 0150 : INITifl.IZED USING 111.JS 1. 0'S 'INIT" ROOTINE. TIEN THE 0160 : QlJASH CHANIELS ARE REFRESHED ANO TIE ffiO KE'IBOORD
0170 :SCAlfED ~ USING ROOTINES FRllf'I MUS 1 9
0180 : Fltfll.LY, THE PIEBUG ROOTINE 'DECOOE' IS USED TO READ TIE 0199 : COl'l'Rll KEYBOARD AN> ANY COl'lfH)5 ARE EXECUTED.
0280 :0-Sl'STEl1 CLEAR fW RE-INITi 1-TlM ALL ClfflNELS;
0219 :2-SET SPLIT POINT, ANY AGO KEY PRESSED BECmES SPLIT 9220
0239 . OR 1009
0240
A5 E8 | 0250 STAR LDR *OUTT | : GET THE 1 OF RESER\IED LON CtflNS
85 EC | 0260 | STA .OUT2 | : SAYE PERl'IANENTL Y
A2 97 | 0270 POSP LDX 97 | : SET UP A POINTER/CllJNTER
A9 911 | 0280 SLP9 LDR 911 | : ANO GET READY TO ZERO STUFF
95 A2 | 0290 | STA *HKEY, X : ZERO THE TEl1PORARY BUFFER
CA | 0300 | DEX | :AND POINT TO THE NEXT
10 F9 | 0310 | BPL SLP9 | : IF SOl'IE ARE LEFT, LOOP
20 21 0D 0320 | JSR INIT | : 111.JS 1. 0 - INTIFLIZE SYSTEl1
29 28 0D 0330 SLP6 JSR l«lTE | : i'JJS 1. 0 - REFRESH AND READ POO KBD
20 09 0F 0340 | JSR DECO | :PIEBlXl - REFC> COl11AND KEYBOARD
F9 EC | 0350 | 8EQ POSP | : IF Cllf'll!Atl) = 9, BRAll:H TO RE-INIT
C9 01 | 0360 | CMP 91 | : 15 COl1lfttl) = 1?
D0 97 | 0370 | BNE NTST | : l«J, BRANCH TO rEXT TEST
A9 2E | 0380 | LDA 2E | : WILL BECOME 11100LE C
20 23 0D 0390 | JSR INIT+02 : USE PART OF MUS 1 9 INITIALIZE
F0 ED | 0409 | BEQ SLP6 | : BRIKH fl.lllYS
C9 02 | 0410 NTST Cl1P 02 | : 15 COl1llAND = 2? | ----...._"
D0 08 | 0420 | BNE SPLI | : NO, BRANCH TO POL Y-SPLIT PROGRAl't
A5 E7 | 0430 | LDA *KTBL +97 : GET THE LOWEST KEY DWli
F9 E5 | 0440 | BEQ SLP6 | : IF NONE ARE DOWN, LOOP
85 R1 | 0450 | STA •SPLT | :SAYE TIE KEY AS THE SPLIT POINT
00 Ei | 0460 | illE SLP6 | : BRffDI 11..lll\'IS

67

## 1280 ********************************* 1290 :~ UOTE5:

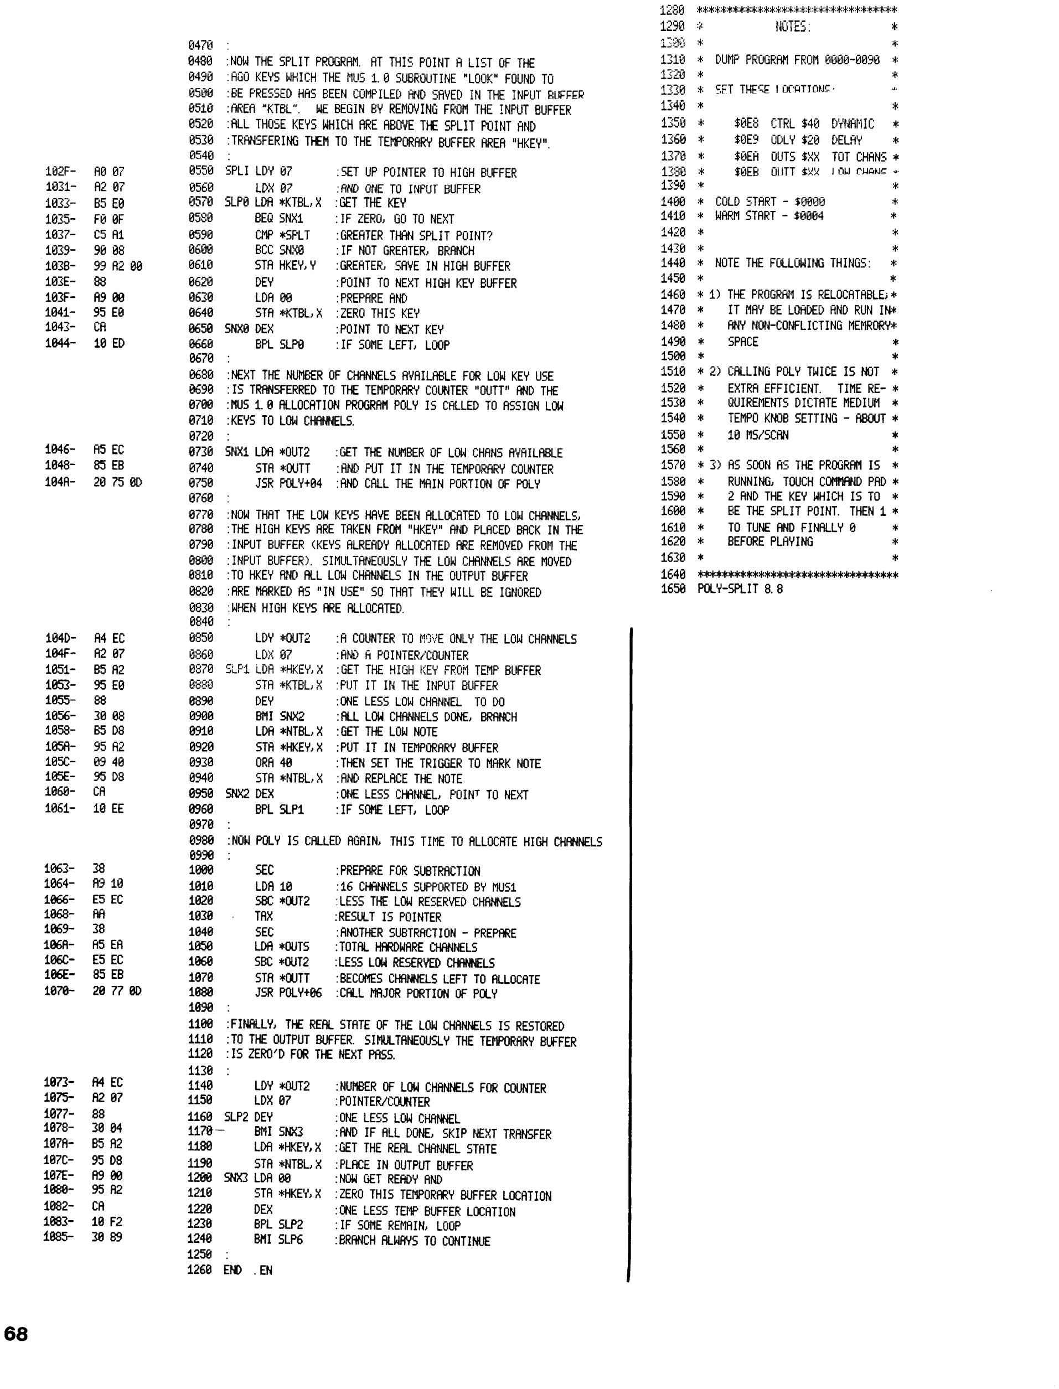
[picture p18: page 2]

0470 | 1:0ü *
0480 : NOW THE SPLIT PROGRAM. AT THIS POHff A LIST OF THE | 1310 * DUMP PROGRAM FROM 0000-0090 * 0490 : AGO KEYS WHICH THE MUS 1. 0 SUBROUTINE "LOOK" FOUND TO | E20 * 0500 : BE PRESSED HAS BEEN COMP 1 LE[l AND SAVED IN THE INPUT BllFl'E:R | rno * SFT THt='C::~ 1 ül'ATH'i,Jb ·
0510 : AREfl "KTBL ". WE BEG IN BY REMOV ING FROM THE ! NPUT BUFFER | 1340 * | * 0520 : ALL THOSE KE'rS WHICH ARE ABOVE TfE SPLIT POINT AND | 1350 * $0E8 CTRL $40 [>'rNAMIC •
0530 : TRANSFERING TfEM TO THE TEMPORARY BUFFER AREA "HKEY". | 1360 • $0E9 ODLY $20 DEUW | • 0540 | 1370 * $0EA OUTS $XX TOT CHANS •
102F- A0 07 | 0550 SPLI LD'r 07 | : SET UP POINTER TO HIGH BlffER | 1380 • t0EB Ol lTT :t~~ | J OLi C'J..JA)J~ ~·
1031- A2 07 | 0560 | LDX 0? | : AND ONE TO 1 NPUT SUFF ER | B90 *
1033- 85 EO | 0570 SLP0 LDA •KTBL, X :GET THE KEY | 1400 • COLD START - $'1000
1035- F0 0F | 0580 | BEQ SNX1 | : IF ZERO, GO TO NEXT | 1410 * WARM START - $0004
1037- | C5 Ai | 0590 | Cl1P *SPLT | : GREATER THAN SPLIT POHff? | 1420 *
1039- 90 08 | 0600 | BCC SNX0 | : IF NOT GREATER, BRANCH | 1430 * 1038- 99 A2 00 | 0610 | STA HKEY, Y : GREATER, SAVE IN HIGH BUFFER | 1440 * NOTE THE FOLLOWING THINGS: | *
103E- 88 | 0620 | DEY | : POINT TO HEXT HIGH KEY BUFFER | 1450 * | •
103F- A9 00 | 0630 | LDA 00 | : PREPARE AND | 1460 * 1l THE PROGRAM 1 S RELOCATA8LE; *
1041- 95 E0 | 0640 | STA •KTBL, X : ZERO THIS KE'r | 1470 • IT MAY BE LOADED AND RUl·I JN.•
1043- CA | 0650 SNX0 DEX | :POINT TO HEXT KEY | 1480 * ANY NOIHONFLICTING 11El1RORY*
1044- 10 ED | 0660 | BPL SLP0 | : IF SOME LEFT, LOOP | 1490 • SPACE | * 0670 | 1500 • | *
0680 : NEXT THE NUMb'ER OF CHANNELS AVAILABLE FOR LOW KEY USE | 1510 * 2) CillLING POLY TWICE 15 NOT •
0690 : 15 TRANSFERRED TO THE TEMPORARY COUNTER "OUTT" AND THE | 1520 * EXTRA EFFICIENT. TIME RE- *
0700 :MUS 1. 0 ALLOCATIOll PROGRAM POLY 15 CALLED TO ASSIGN LOW | 1530 * QUIREMENTS DICTATE MEDIUM *
0710 : KEYS TO LOW CHANNELS. | 1540 * TEMPO KNOB SETTING - ABOUT *
0720 | 1550 • 10 MSISCAN
1046- A5 EC | 0730 SNX1 LDA •OUT2 | :GET THE NUMBER OF LOW CHANS AVAILABLE | 1560 • | * 1048- 85 EB | 0740 | STA •OUTT | : AND PUT IT IN THE TEMPORARY COUNTER | 1570 * 3) AS SOON AS THE PROGRAM 15 * 104A- 20 75 0D | 0750 | JSR POL'r+04 :ANO CALL THE MAIN PORTION OF POLY | 1580 | RUNNJNG, TOUCH COMMAND PAD *
0760 | 1590 | 2 AND THE KEY WHICH 15 TO *
0770 : NOW THAT THE LOW KE'IS HAVE BErn ALLOCATED TO LOW CHANNELS, | 1600 | BE THE SPLIT POINT. THEN 1 *
0780 :THE HIGH KEYS ARE TAKEN FROM "HKE~"' AND PLACED BACK IN THE | 1610 | TO TUNE AND FINALL Y 0
0790 : INPUT BUFFER (KEYS ALREAD'r ALLOCATED ARE REMOVED FROM THE | 1620 | BEFORE PLAVING
0800 : INPUT BUFFER). SIMULTANEOUSL'I THE LOW CHANNELS ARE MOVED | 1630 * | * 0810 : TO HKE'I ANO ALL LOW CHANNELS IN THE OUTPUT BUFFER | 1640 ********************************* 0820 :ARE MfiRKED AS "IN USE" 50 THAT THE'r WILL BE IGNORED | 1650 POLY-SPLIT 8. 8

0830 WHEN HIGH KEYS ARE ALLOCATED.
0840
1040- A4 EC | 0850 | LDY •OUT2 | : A COUNTER TO M'WE ONL Y THE LOW CHANNELS
104F- A2 07 | 0860 | L[>i< 07 | : ANü fi POHITER/COUNTER
1051- 85 A2 | 0870 SLP1 LDA •HKEY, X : GET THE HIGH KEY FROM TEMP BUFFER
1053- 95 E0 | 0880 | STA •KTBL, X : PUT IT IN THE ltlPUT BLIFFER
1055- 88 | 0890 | DEY | : ONE LESS LOW CHANNEL TO DO
1056- 30 08 | 0900 | BMI SNX2 | : ALL LOW CHANNELS DONE, BRANCH
1058- 85 08 | 0910 | LDA •NTBLX : GET THE LOW NOTE
105A- 95 A2 | 0920 | STA •HKEY, X : PUT IT IN TEMPORARY BUFFER
105C- 09 40 | 0930 | ORA 40 | : THEN SET THE TRIGGER TO Mf!RK NOTE
105E- 95 DS | 0940 | STA •tHBLX : ANO REPLACE THE NOTE
1060- CA | 0950 SNX2 DEX | : ONE LESS C~NNEL, PO !NT TO NEXT
1061- 10 EE | 0960 | BPL SLP1 | : JF SOl'IE LEFT, LOOP
0970
0980 : NOW POLY 15 CALLED AGA IN, THIS TIME TO ALLOCATE HIGH CHANNELS 0990
1063- 38 | 1000 | SEC | : PREPARE FOR SUBTRACTI ON
1064- A9 10 | 1010 | LDA 10 | : 16 CHflNNELS SUPPORTED BY MUS1
1066- ES EC | 1020 | SBC *OUT2 | · LESS THE LOW RE~.ERl/ED CHANNELS
1068- AA | 1030 | TAX | : RESUL T 15 POINTER
1069- 38 | 1040 | SEC | : AMJTHER SUBTRACTION - PREPARE
106A- A5 EA | 1050 | LOA •OUTS | : TOTAL HARDWARE CHANNELS
106C- E5 EC | 1060 | SBC •OIJT2 | : LESS LOW RESERl/EO CHANNELS
106E- 85 EB | 1070 | STA *OOTT | : 8ECOl'IES CHANNELS LEFT TO ALLOCATE
1070- 20 77 0D | 1080 | JSR POLY+06 :CfU MAJOR PORTION OF PCX.Y
1090
1100 : FINALLY, TfE REAL STATE OF THE LOW CHANNELS 15 RESTORED 1110 :TO THE OUTPUT BUFFER. SIMULTANEOUSLY THE TEMPORARY BUFFER 1120 : 15 ZERO'O FOR TfE NEXT PftSS.
1130
1073- A4 EC | 1140 | LDY *ÜUT2 | : NUl'IBER OF LOW CHANNELS FOR COUNTER
1075- A2 07 | 1150 | LDX 07 | : POINTER/COUNTER
1077- 88 | 1160 SLP2 DEY | : ONE LESS LOW CHANNEL 1078- 30 04 | 1170- | BMI SNX3 | :AND IF ALL DotE. SKIP NEXT TRANSFER
107A- 85 A2 | 1180 | LOA •HKEY,X : GET THE REAL CHANNEL STATE
107C- 95 DS | 1190 | STA •NT8L, X : PLACE IN OUTPUT BUFFER
107E- A9 00 | 1200 SNlG LOA 00 | : NOW GET READY AND
1080- 95 A2 | 1210 | STA *HKEV. X : ZERO THIS TEMPORARY BUFFER LOCATION
1082- CA | 1220 | DEX | : ctlE LESS TEMI' BUFFER LOCATION
1083- 10 F2 | 1230 | 8PL 5LP2 | : IF SOME REMAIN, LOOP
1085-- 30 89 | 1240 | 8111 5LP6 | : BRANCH ALWAYS TO CONTINUE
1250
1260 END . EN

68
