Skidlz/PAiA-8700/Tape Programs/Echo/Echo.pdf

ECHO ... ECHO ..... ECHO | „ |

A couple of issues ago, I
said that we were going to look at a D/A that would allow those of you with exponential response
synthesis | equipment | to begin
playing | with | the | computer
software we have been discussing here. Then SEQUE ran langer than I thought it would, and we ran into logistics problems and

In any case, it's not ready yet. Next time for sure. Meantime, l've got some quickie code that I tbink you'll

like, It's a program we call ECHO. 1 1 11 bet you tbink that ECHO echoes. lt does.
lt works in conjunction witb an allocation algorithm (POLY from MUS 1 in tbis case, though something like Bob Yannes' SHAZAM could also be patched in to use tbis) and "follows" wbatever data

is being produced from QuASH channel U1, delaying it for a
controllable | period | of | time
before playing it from a second cbannel, delaying again before playing an a tbird channel, and so an.
A | convenient | conceptual
handle | tbat | may | belp | you
understand tbe "bow-it-works" of ECHO might be a clock face. With only a second band.
The numbers around tbe clock face represent memory locations and tbe second hand represents a pointer to tbese memory locations

whicb, as it sweeps past eacb
number, writes | whatever | note
happens to be coming out of QuASH channel #1. Tbis is really a funny clock, tbougb, because in addition to tbe single second band it has many minute bands tbat rotate at tbe same rate as tbe second band. If tbe second
hand | is a "writing pointer",
tbese funny minute bands | are
"reading pointers". Witbin some restrictions tbat we'll discuss sbortly, we can have as many reading pointers as we like; tbe important feature is tbat eacb of
tbese | fast | | minute | bands
correspond to an additional QuASH cbannel.
Now as tbe clock runs, the writing pointer scans merrily tbrougb memory, writing the note tbat's in cbannel #1. In step
bebind | it | are | tbe | reading
pointers, and. as tbey point to successive memory locations tbey read tbem and,place the result in the QuASH channel to whicb tbey correspond. Presto; ecbo :- · ·
In computerese, this kind of procedure is called a queue.
ECHO bas a | variety | of
software control features, and since I don't really know wbich of them are more important, we'll just plunge into tbe middle. While ECHO always pulls tbe note tbat it's going to ecbo from channel #1, tbe first channel that tbe ecbo effect appears an doesn't have to be cbannel #2. Why? So tbat some cbannels can be set aside for polypbonic work wbile otbers are producing tbe ecbo.
Here's how. One piece of
data | tbat | every | polypbonic
allocation subroutine must have is the number of output cbannels
available | for | its use. POLY
established the precedential name OUTS for tbis datum and set its

location in a Paia 8700 as $EA. Previously, we've always set this variable· to represent the number of QuASH cbannels tbat were bardware supported. In a system wbicb bad a single QuASH,

OUTS was set to contain $04 so tbat all available outputs were used for polyphonic allocation.

But OUTS may be set equal
(may I | please | start | saying
"equal" instead of "contains"? It's not strictly true, but mucb less cumbersome.) to a number less tban tbe number of hardware supported cbannels and tbe result will be to reserve some channels. In a system witb two QuASH (for example) OUTS could be set equal to $05 and tbe result would be that tbe upper 3 channels (6 - 8)
will | not | have | keyboard
activations directly assigned to tbem. POLY (or whatever) doesn't know tbey're tbere.
So we can use tbem for other tbings. Like echo channels. ECHO, in its turn, must know bow many cbannels it bas to work witb. The location labeled ECCO ($BB) serves this function, and. in most cases will be set equal
to | the | number | of remaining
channels.
To give a final example; if we make OUTS equal to $03 and ECCO equal to $05, we've produced a system which has 3 polyphonic

channels (the first three) with channels 4 through 8 echoing, in sequence, the notes that appear an polyphonic channel #1.

I would be less than candid if I didn't forewarn you that successful use of a system which combines both polyphonic and echo
channels | requires | a thorough
understanding of the allocation
algorithm being used as well as a certain | manual | and | mental

dexterity. It's best to start
playing | with | a configuration
which has | only | one | channel
available | to | POLY | and | the
remainder used as echo channels. With practice, you can progress from there.

# DELAY CONTROLS

As you certainly know by
now, all timing in our system references back to tbe scan rate of the keyboard, and ECHO has associated with it a variable
53

labeled | EDLY | ($BC) | which
regulates how fast (in terms of keyboard scans) the hands in our clock analogy (the reading and writing pointers) advance from one memory location to the next,

which in turn contributes to how long the echo delay is.
If we set EDLY equal to $01, the echoing routine is invoked after every keyboard scan (which is variable, but typically will be every 10 to 50 milliseconds). Making EDLY equal to $02 means
that | the routine is used on
alternate | scans | | which, | if
everything else is equal, will produce an echo delay twice as long.

Notice that this affects
only the ECHO and does nothing to alter POLY's allocating channels after every keyboard scan. This
is | important | because | when
changing the value of EDLY you should be aware that if you skip more than about 8 scans before

invoking ECHO, it may miss some keyboard activity in a fast riff.

The notes will still play through
the | polyphonic | channels, but
won't be echoed.
A second | variable | also
interacts with EDLY to detirmine
the echo | delay. | OFST | ( $BD)
controls the offset between the pointers into the echo queue.
Going | back | to | the | clock
metaphore, it detirmines how "far apart" the hands on the clock are. The farther apart they are (the bigger the number in OFST),

the greater will be the echo delay.
Like EDLY, there are some caveats that go with OFST. The
echo buffer (queue) | area | of
memory is 6~ bytes on page 1. You
don 1 t want. '"~ | anme •m wi.th too
many pointers | {controlled | by
ECCO, remember) that are too far apart or they will represent a memory area larger than that set aside. The result of that is far from disastrous, but it will cause things like the high order

channels echoing müch sooner than you expected, as the reading pointers for those channels "wrap around" past the writing pointer. But, as we've decided here in the
past, the | difference | between
noise and a neat effect is orten nothing more than a creative mind.
Control of the time delay
involved in the echo is important for reasons that you might not first think about, because like any device (or now software) that messes with the subjective flow

54

of time, echo offers a variety of
totally | different | effects
depending on how long a time we are talking about.
For example, if the delay is very short, as when both EDLY and OFST are set to $01 1 the effect
will not even be percieved as an echo, | but | rather | as | a "thickening" of the voice (voice

doubling, actually). It's a lot like phasing or flanging, except that with those techniques the predominant effect is frequently that the subjective flow of time is cyclicly changing.
Longer delays (EDLY = $01
and OFST = $08) produce the types
of effects which give ECHO its name. Echoplex | type | echoing.
There | is a major difference,
though, in that with conventional echo devices you can only echo in a voice that is essentially the

same as the starting voice. Here, the echoes can be anything, and there's no way to appreciate the power that. this implies without working with it.
When the delays get very
long (EDLY = $02 and OFST = $10) you find yourself playing with an instrument that allows you to play rounds with yourself. Also, of course, in different voices. Because the character of the
instrument | is | so | greatly
influenced by delay times, and because the different characters can so frequently be used in the same musical performance, we've
added | a | means | of | quickly
switching | from | one | set | of
operating parameters to another.
Four | of | these | presets | are
provided | by pads 0-3 on the
command keyboard. Touching one of -these pads causes ECHO to get the requested set of parameters from a table that lives in memory $9A

$A9 and place them in the
locations referenced by the rest of the program. The pre-sets that are in place in the listing which

follows are:

COMMAND POLY | ECHO | TIME DELAY
KEY | CHANS CHANS (KBD SCNS)
0 | 7 | 1
1 | 7 | 8
2 | 3 | 16
3 | 3 | 32

Notice a couple of things
here. First, if you're using a system with only a single QuASH

(a P4700/J or its equivalent) it doesn't matter that there are more echo channels than there are hardware channels; the last four iterations simply won't have the hardware to voice them. Secondly, observe that when we got to longer delays we cut back on the number of echo channels so as to circumvent the "too many channels too far apart" problem that we looked at earlier.
You can substitute your own presets for those shown simply by altering or replacing the values shown. Here is a map of locations that will make that a little easier:

PRESET #
| 0 | 1 | 2 | 3
OUTS | $9A | $9E | $A2 | $A6
ECCO | $9B | $9F | $A3 | $A7
EDLY | $9C | $AO | $A4 | $AB
OFST | $9D | $A1 | $A5 | $A9

With some experimentation
you will find echo presets which seem to complement each other
particularly | well. | You | will
inevitably get to where you use a specific set of presets for each
particular | song, | not | only
changing presets throughout the song but within a riff or phrase. This can create some neat effects such as having an initially long delay set and, in the middle of the echo chain, hit a faster preset to initiate a burst of echoes. Or, have one preset for the "voice doubling" character-istics we discussed. Then you can switch between echoes for special effects and doubling for use on bass lines or solos.
Actually, there is a lot of power hidden in this program that can be liberated with innovative patching, voicing, and mixing. How about having a chain of voices which are all related but
slightly | different, | such | as
having higher Q on the filters as
the echo is | passed | on. | Or
changing envelope times so the first echoes have sharp attacks and delays and later voices have increasingly softer envelopes. Here's a good one- progressively detune each voice so you get a spiraling echo, or the echoes

sequence upscale (or downscale).
Completely different voices can be used, and | this | technique

really works well on the long delays for doing rounds.
Just playing with the mixing or panning of the normal echo

voices can entertain you for hours. Have the echoes pan across the stereo field, or bounce back and forth. Or have the echoes begin to fade out, but set the last or next to last voice at a

higher level.
You can also use a multi- voice setup with only a few of the outputs dri ving voices. Set up the computer to provide ( for example) one poly voice and seven echo voices, but only use channels 1, 4, 5, and 8 to drive oscillators. Work with various combina tions here; each is a completely different rhythm and could easily provide a rhythmic basis for a whole piece.
Well, by now you are probably ready to dig into the program, so here is the listing.

00&-
003-
005-
.096-
808-
00A-
00()-
80E-
.w.e-

913-
015-
017-
018-
019-
018-

01D-01F-021-
023-
025-
027-
028-
02A-
02C-

02E-030-
033-
035-

LOADING THE PROGRAM
As with other programs that we 1ve examined in the past, ECHO may be band-loaded using the 8700 computer' s monitor,

but first set the moni tor stack pointer: 0-E-D-DISP-F-F-ENT
and the user' s stack pointer and status register: O-F-E-DISP-F-F-ENT-0-0-ENT

and then load the program: 0-0-0-DISP-2-0-ENT-2-1-ENT-8-D-ENT- (etc.)
and don't rgß~'.:t ~~is ~at~ ba4~ ig~or~~ti~~: 07
090- DO 05 AO 5C 20 52 OD 4C 098- 10 10 01 | 07 01 | 01 | 01 | 07
OAO- 01 | 08 01 | 03 02 08 01 | 03 OA8- 02 10
OB8- FF FF 01 | 03 02 04 OE8- 40 20 01 After loading (and before running) the program and data should be dumped to tape (from location $000 to $0EC) using this sequence: 0-0-0-0-0-0-E-C-0-1-D-D-TAPE
When this tape is loaded in the future, | i t should be
loaded from $000 to $0EC so that the presets will be loaded along wi th the pro gram.

28 21 00
A2 FF
9A
A9 00
A2 3F
9() 00 02
CA
10 FA
28 71 00

A0 eF
A6 Eli
88
CA
D0 FC
04 EB

A6 BE
C6 EC
D0 09
A5 BC
85 EC
CA
10 02
A2 3F
06 BE

A5 OF 9() 00 02

A5 88
85 BA

0010 : **********************+********* 0020 :•
0030 :• | ECHO 0. 31 | •
* *
0&10 :•
POLYPHONIC VOICE lllJEUING
:• | * 0050 :• 0060

0070
0080
0090
0100
0110
. ~ | . :* | 'JCHl Sll'IJNTON | •
:• | | | *
:O(C) 1979 PAIR ELECTRONICS, INC• '* fl.L RIGHTS RESERYED
0128 :• | • 0130

0140
0490
0500
0510
0528
0530
0540
0550
0560
0570
0580
0590
0600
0630
0640
0650
8660
0670
0680
0690
0700
0710
0720
0730
0740
0759
0760
0770
0780
0790
8800
0810
0820
0830
0840
0050
0860
0870
0880
0890
0900
0910
0320
0930
0940

: ********************************

: INIT!fl.IZE S'ISTEM, CLEAR OUTPUT BlHERS fffl ECHO BlfFER

STAR JSR INIT
LDX eFF
TXS
EBZR LDA 00
LDX 3F
ILP STA EBlF, X
DEX
BPl ILP
ECHO JSR POLY

: CALL MUS1 INITlfl.IZATION
: PREPARE TO SET STACK POlllTER
: SET STACK TO TOP OF PAGE
: PREPARE TO ZERO ClJT ECHO BIFFER : POillTER TO END OF ECHO BUFFER : ZERO ECHO SUFFER LOC:ATION :POINT TO NEXT LOCATION
:NGT DONE \'ET, LOOP
:Cfl.L MUS1 POL'IPHONIC ALLOCATION :DETERl11NE AOORESS OF TIE FIRST CHFHlEL A\IAILFBLE : FC:R ECHO U5E

LDY eF
LDX •OUTS
LP0 DEY
DEX
BIE LP0
STV .cllTT

:OFFSET TO FIRST OUT-BUF LOCATION : lfJMBER OF POL YPHONIC CHANNELS :POINT TO NEXT OUTPUT CH/HEL
: ONE LESS POLY ClflNNEL
:fl.L POLY Ctfl6 NOT USED, LOOP :SAYE FIRST ECHO POINTER FC:R LATER

:Al>YfflCE ECHO Bll'FER POINTER AN0 Al>JUST IF NECESSARY

LDX *EPNT
DEC •CNTR
BNE GETN
LDA •EDLY
STA •CNTR
DEX
8PL GETN
LDX 3F
GETN STX •EPNT

:GET CURRENT ECHO BUFFER POINTER : DECREl'IENT TIMER
: Til'E NOT UP, BRANCH
:TIME UP, RE-INIT Tll'IER Vfl.UE :RE-INITIALIZE TINER
:POINT TO NEXT
:BRANCH IF STILL MITHIN BUFFER AREA :OTIERWISE, RE-INIT POINTER
: 5AYE NEW POINTER

:PUT ClMll!ENT CHANNEL 1 NOTE IN ECHO BUFFER AND : PREPARE ECHO CtflNNEL COUNTER

LDA >IC!fl1
STA EBlf, X
LOA *ECCO
STA *TEl'IP

: GET CHANNEL 1 NOTE
: 5AYE IN ECHO BUFFER
: GET NLttBER OF ECHO CHANNELS : SAVE AS CCWTER

:CAL.ClLATE SUCCESSIVE ECHO BUFFER LOCATIONS AND

037- | 8A
038- | 18
039- | 65 BD
038- | C9 40
03D- | 90 03
03F- | 38
040- | E9 40
~42- | AA
043- | BD 00 02
046- | 99 00 00
049- | 88
04A- | C6 BA
04C- | D0 E9
04E- | 20 28 0D
051- | A4 EB
053- | A6 88
055- | A9 00
057- | 99 00 00
05A- | 88
058- | CA
05C- | 00 F9
05E- | 20 00 0F
061- | C9 04
063- | 10 18
065- | 8C 20 08
068- | A9 FF
06A- | 18
068- | 69 04
06D- | 88
06E- | 10 FR
070- | AA
071- | Fl0 03
073- | 85 9A
075- | 99 BA 00
078- | CA
079- | 88
07A- | 10 F7
07C- | 85 EA
07E- | 30 90
080- | F0 7E
082- | C9 06
084- | 30 80
086- | D0 06
088- | 20 21 01)
088- | 4C C0 FF
08E- | C9 07
090- | D0 05
092- | Fl0 5C
094- | 20 52 00
097- | 4C 10 10

0950 : AOJUST AS NECESSARY 0960
0970 LP1 TXA
0980 | CLC

: ECHO BUFFER POINTER TO ACCUMULATOR : PREPARE FOR ADDITTION
0990
1000
1010
1020
1030 | ADC •OFST CMP 40
| BCC SAVE SEC SBC 40

1040 SAVE TAX
1050

:CALClLATE NEXT LOCATION : STILL WITHIN ECHO BUFFER?

: YES, BRANCH TO CONTI NUE
: NO, SET CARRY FOR SUBTRACTION : ANO AOJUST POillTER
PUT POINTER IN PLACE

1060
1070
1080
1090
1100
1110
1120
1130 | : THEN PULL NOT ES FROM ROTATED ECHO BUFFER LOCATI DNS : AND PLACE IN ECHO CHANIELS OF OUTPUT BUFFER ( NTBU

1140

LDA EBUF, X
STA NTBL, Y
DEY
DEC •TEMP
BNE LP1

: GET NOTE FROM ECHO BUFFER
: PLACE TO OUTPUT CHAHL
: POINT TO NEXT OUTPUT CHANNEL : ONE LESS ECHO CHIHEL
: BUT SONE LEFT, LOOP

1150 : NOTES ARE PLAl'ED BY Cfl.Llt-«l THE lllJASH DRIYER <NOTE). 1160 : FI NALL Y, ECHO OUTPUT CHAlffLS ARE CLEAREO SO AS NOT 1170 : TO COlfUSE POLY 1-t!EN CALLED
1180
1190
1200
1210
1220
1230
1240
1250
1260
1270
1280
1290
1300
1310
1320
1330
1340
1350
1360
1370
1380
1390
1400
1410
1420
1430
1440
1450
1460
1470
1480
1490
1500
1510
1520
1530
1540
1550
1560
1570
1580
~590
1600
1610
1620
1630
1640
1650
1660
1670
1680
1690
1700
1710
1720
1730
1740
1750
1760
1770
1780
1790
1800
1810
1820
1830
1840

LP2

JSR NOTE
LOY •OUTT
LDX •ECCO
LDA 00
STA NTBL Y
DEY
DEX
BNE LP2

: CALL MIJS1 QUASH DRIVERS, ETC. : GET FIRST ECHO CtflNNEL POINTER : GET 1 OF ECHO ClflNNELS
: PREPARE TO ZERO
: ZERO ECHO ClJTPUT CHANIEL
PO !NT TO NEXT OUTPUT
: ONE LESS ECHO CHAlffL
:SOME LEFT, LOOP

:READ COMMANOS. 0-3; PRESETS, 4-iNITIALIZE S'ISTEH : 5-CLEAR ECHO, 6-BREAK, 7-TUNE

JSR DECD
CMP 04
BPL NEXT

: READ COMt"lfK> KE'IBOARD
: IS COMMAND A PRE-SET?
: NO, BRANCH FOR NEXT TEST

: THE Clllt1AND IS TO CALL UP A PRE-SET. fflER Cfl.LCLATll«l : TIE BASE Al>DRESS OF THE PRE-SETS Cfl.LED FC:R, TIE PRESET : Vfl.UES ARE TRANSFERED TO THEIR RESPECTIYE LOC:ATIONS
: AS ACTI VE PARAMETERS. NOTE THAT THE NUl'IBER OF :CHANNELS ALLOCATED TO POLY USAGE <OUTS - S00EA) IS IN :NON-CONTIGUOUS LOCATION AND l'tUST BE HANDlED SEPARATELY : NOTE THAT THE CONTIGUOUS LOCATION •TEl1P IS USED AS A : DlNIY YARIABLE AT THIS POlllT

LP3

LP4

STY DISP
LOA eFF
CLC
fl)C 04
DEY
BPL LP3
TAX
LDY 03
LDA •PRST,X
STA TEtf', Y
DEX
DEY
8PL LP4
STA •OUTS
8111 ECHO

NEXT BEQ STAR
Cl1P 06
Biii EBZR
8NE NXT0
JSR INIT
JMP BRAK
NXT0 CMP 07
BNE BRDG
LDY 5C
JSR FILL
BRDG JMP ECHO

: SHOW PRESET
: ONE LESS Tfftl PRESETS BASE fl>ORESS : PREPARE FOR Cfl.ClA..ATION
: THERE ARE 4 PRESET VARIABLES
: PO !NT TO NEXT PRESET BASE
: IF NOT THIS PRESET, LOOP
: PUT POINTER Cfl.ClA..ATED TO X :4 PRESETS, WILL CCWT TO -1 : GET PRE-SET DATA
: AND PLAGE AS ACTIYE PARAIETER :POINT TO NEXT PRESET DATA :AND NEXT ACTIYE PARAIETER
: 1 F NDT 'IET DCJNE, LOOP
: SAYE THE 1111/ERICK PARAIETER
: BRfKH fl.WA'IS

: CotttfN) IS FC:R CLEAR, BRANCH
: 15 COl1fH) 5 <CLEAR ECHO) tR 6 <BRIO? : COl11llll) 1 S CLEAR ECHO, BRANCH :COl'tlAND IS l()T BRK, BRIKH
: SHUT DOWN SYNTIESIZER
: Alll RETURN TO l'IJNITC:R
: IS COl't1AN() Tl.NE?
: A BRANCH TOO FAR
: PREPARE TO TU!E TO MIOOLE C : SEE l'IUS 1. 0 OOC!KNTATI ON
: PLA'I ON ANl ON AND ON

:SET-UP YARIABLES FOR l'IUS1
. OR 108A : INITIAL PRE-SET
. HS 01030204
. OR 10E8 : S'ISTEM CONTROL AND QUASH DELAY . HS 402001 : AND OUTS
: AND PRESETS
. OR 109A
. HS 01070101
. HS 01070108
. HS 01030208
. HS 01030210

END . EN----------------
55
