Skidlz/PAiA-8700/EPROM Programs/MUS-1/MUS1.pdf

# LAD NO T~S ; Mus , by John s. Si~owo, i'·

w~h the new miracle in;redient - st;

With the exception of the bare-bones | The QuAsh drivers (called NOTE)- | change from one value to the next and
Usting of POLY l. o that ran in the last | same thing- we're going to need them for | if appropriate settling time is not allow-
issue, we haven't looked at any software- almest everything we do. Why bother to | ed between writes to the QuAsh channels
mainly because there was little to examine. load them? | we will be able to hear the changes as a
But MUS l was just recently finalized, | In addition to these two routines, MUS 1 slight 11 buzz¹¹ in each of the channels.
so that situation is beginning to change. | also contains: | The Solution here is to output the data
MUS 1, for the benefit of those of you | INIT: an initialization routine that takes first to a 11 dummy channel" that is
who haven't been waiting for it for the | care of setting various variables and buf- occupied solely by the D/ A, with no
last six months, is what many would call | fer areas to a known, acceptable state | corresponding QuAsh, followed immedi-
"system firmware"- and since that has | (as opposed to the random numbers they | ately by a write of the identical infor-
the sort of technical ring to it that tends | will contain when power is first applied.) | mation to an output which does corres-
to make things interesting, we'll call it | POLY: essentially the polyphonic (1 | pond to a QuAsh channel. The first
that, too. | still prefer polytonic) allocation algo- | write allows the D/A to settle while the
In almost any computer application | rhythm from POLYl. O, except refined | second strobes the settled output into
there are some programs which, for one | somewhat to take less memory space. | the appropiate QuAsh channel.
reason or another, are best handled as | TRGN: The new miracle ingredient- | And here we come face to face with
firmware- a name that these days means | Software Transient Generators (STG). | the next problem; the QuAsh really need
not software (which must be loaded from | A routine that will serve as a software | some settling time since they are at
some storage media external to the com- | substitute for ADSRs. | their heart nothing more than an RC
puter) and not hardware (a permanently | OPTN: A very simple option selecting | circuit.
wired collection of gates, etc. which | program that allows the remaining firm- | As Iong as we are thinking in terms
cause a specific, set sequence of actions | ware of MUS l tobe tied together into a | of small systems(8 output channels ar:
to take place) but something betwixt and | 16 voice polyhonic synthesizer with or | less) this is not a big problem since it
between; most usually, software that is | without software transient generators- | can be dealt with simply by delaying af-
contained in a PROM somewhere. | without having to lead ~ additional | ter writing to one QuAsh but before set-
The most obvious firmware is a mon- | software (though several parameters will | ting up the next. 1f the delay is not long
itor program such as PIEBUG. Since | need tobe initiallized manually), | enouglj., we will hear changes from one
this program is the thing that allows for | All of this is pretty straight-ahead | value to the next not as an instantaneous
the entry of data and instructions into | code that should be understandable from | change, but rather as a series of steps
the memory of the Computer in the first | the documented Usting that appears at | from the initial value to the final one:
place ever de-bugging

(as well as and
usually editing

providing features

what- the | the
| refer end
| back of this
| to previous article-
| articles you may
| in need
| this
| to | Ll= lc J
designer thought were important and/or | series for background information; "In | vt | l | v!
had room for), it is at least inconvenient | Pursuit of the Wild QuAsh " (reference | | _J
to have to load it every time it is needed. | Polyphony, July '77) and "What the Com-
Much better to have it in a dedicated | puter Does" (reference Polyphony 4/76)
PROM where it is always available for | would be particularly useful ones. | | T->
| | | We want this

T-+

immediate use. | Two exceptions,. NOTE and TRGN,
The fi.rmware of MUS 1 is roughN an- | need some additional explanation - they | figure a | | But if the QuASH settling delay is not long enough, will get this.
alogous. These are universally useful | introduce some new ideas.
routines that, with rare exceptions, will | In an embryonic form, NOTE was a
be used with everything we do musically. | part of POLY l. O. lt is the responsibil-
lt's a waste of ti.Ire and resources to have | ity of this routine to take individual en-
to load them to RAM from tape (or worse | tries from the output buffer area (NTBL),
yet, manually) every time they're needed. | add to it the corresponding entry from
A PROM is their happiest home. In our | the Transpose buffer area (TTBL)and
8700 Computer/Controller, MUS 1 is a | output the results to the QuAsh channels.
l 702A PROM that occupies the address | Seme aspects of the significance of the
range $DOO-$DFF (IC-17). | addition that takes place will be seen
Examples? OK, the keyboard read- | when we look at TRGN- for now, it will
ing routine (LOOK). lt isn' t particularly | suffice to say that this will be an extra-
long or complicated (a little over 30 | ordinarily handy convention in a number
bytes) but we're going to need lt every | of cases.
time we turn on the system- even if it | A more important function of NOTE
isn't used to read the keyboard, it's the | is to make sure that what comes out of
thing that our protocols tlictate will be | the QuAsh channels has no annoying
the tempo-determining element in the | glitches that may be artifacts of the D/ A
system (based on the clock rate of the | and multiplexing process. In an earlier
encoder). At some future date the oc- | story, we looked at one of the annoyances
casion may arise when we can examine | - the fact that our 8780 D/A, though
this in detail. Today, it's not the point. | quick, takes a flhlte amount of time to

In larger systems, this constant delay approach is not a practical solution because there is not enough time during altemate "dummy" scans of the keyboard (the time which our conventions allow for processing, output driving, allocations, etc. ) to allow .!!:!! of the output channels the luxury of a delay. The time comes for the keyboard tobe read again (or other things to happen) and the processor is still busy waiting for all of those QuAsh to get to the right value.
The key to the Solution of this problem is to notice that there is really only one set of circumstances under which the long QuAsh-settling delay is required, and that's when the output of one of these channels must change from one value to another (which happens only a small percentage of the time) and then, only when the glide of the channel is turned off. (if the glide is on, its integrating action will smooth out the steps; and, in fact, a short write time is preferable here since it will serve to increase the time required for the glide. )
The actual solution is what 1 feel we should call "DYNAMIC QuAsh DRIVERS" -a small block of programming, more or less in the middle of NOTE.
This part of tre program first checks to see if the glide control bit (the most signüicant bit of the data just written to D/ A and S/Hs) was turned on or not. If we are in "glide mode," no delay is required so the program immediately goes to see if there are any channels left to write; if there are, it services them.
lf the glide is not on, we have a candidate for dynamic operation so the dynamic mode switch is checked (more later) and if this option is selected the current data is compared to the data that was previously written to this channel ( requires a new table that we1 ve generated called "LAST") and if they' re different ( a change), the program goes into the delay that allows the output of the QuAsh to instantaneously (apparently) step from its previous value to the next one. The lilew value is saved in LAST (for use next time) and if there are more channels to do- it does them.
SOFTWARE TRANSIENT GENERATORS

Here we begin, for the first time, to replace some of the elements that constitute traditional synthesizer hardware with software that performs the same function (hopefully as well, or better) with less costly hardware. STGs are a good place to start because they're not super difficult to implement.
Just like their hardware equivalents, STGs respond to a note which has just been triggered ( pressed on the keyboard) by producing a voltage that rises at a controlled Attack rate. After reaching some peak value, the voltage then drops at a Decay rate until it reaches
a pre-set Sustain level where it stays as long as the note remains triggered. When the key is released, the voltage drops to its lowest level at the Release
rate. | ~~~
Computing the number which represents the current value of the transient is only slightly more complicated than adding, subtracting and comparing. Unlike an ADSR, an STG has no knobs to set, in their place you enter numbers setting Attack rate, etc. into the computer.
Perhaps the biggest problem having to do with STGs is deciding where they should come out. Oh, the QuAsh channels, obvio1Bly; but which ones? Of the numerous possibilities, we've selected the convention of having pitch setting voltages (those that correspond to notes) and transient voltages come from alternateQuAsh channels, primarily because this will work nicely with some stuff under development (or consideration, at least), without making obsolete all of the hardware that we've accumulated up to now.
This implies two distinct modes of operation; the first in which the STGs are not asserted and POLY assigns notes to sequential QuAsh channels; and, the second mode ( STGs on ), in which notes are assigned by POLY* to the odd number QuAsh channels ( first, third, etc.) while transients are produced at the even number outputs (second, fourth, etc.).
The note produced at the first QuAsh output has a corresponding transient happening at the second output, and so on. Just as if the trigger from the first channel were patched to the input of an ADSR whose output was somehow tied to the output of the second QuAsh channel.
This would seem a good place to mention (in case it's not already obvious) that in this implementation all of the STGs produce the same kind of transient, and for the kinds of things that we're doing now, this is how it should be. lt may also be worth mentioning that while the transients are all the same, they are totally independent where following the triggered and released states of their resiective note channels is concerned.
There are also some internal details which muddy the STG waters. For instance, a key that is currently down may require a transient function that is either in the Attack cycle (increasing) or Decay/Sustain cycle (decreasing or holding) depending on its past history (had it already peaked ?). Somewhere we need to save information on which cycle the transient is actually in.
Another, somewhat interrelated, problem concerns the smoothing of the transient waveform. Under most conditions, the glide of the QuAsh channels that are being used as transient outputs should be turned on so that a smoothly increasing or decreasing function is produced. But, the glide can't always be on because that would limit the ma.ximum attack rate. Without having the space to cover it entirely, 1 can only state that the solution to both of these difficulties lies in the use of the Transpose table and remembering that the data stored in TTBL entries is added to the output parameter in NTBL (where we're storing the actual current * Note that POLY checks to seeif the STGs are turned on as it assigns notes to outputs.

value of the transient) before the output operation takes place. Note also tliat while the data in NTBL is manipulated extensively by POLY and TRGN (as they calculate, allocate, - regurgitate ?) TTBL is untouched by computer hands, and this makes it an ideal place to save control type functions. Not only transpositions, but a place that glide and trigger bits and such can be permanently set.
These locations are so handy for this application that in TRGN they have been re-named CWRD (Control-Words, •. but do not be confused, this is still our old friend TTBL and has no relationship at all to the System Control Word-CTRL) and it is here that we keep track of the A/D/S state of each of the transient channels.
Also, to help me keep things straight in my own mind, the NTBL bytes that are used to store the current value of the transient have been re-named PARM (parameter); but, agr.dn, this is the same physical area as NTBL.

NOW, HOW DO WE USE ALL THIS?

Perhaps the best way to begin an essay on how to use MUS 1 is to state one of the functions that it was devised to perform As you are no doubt beginning to realize, we've carefully developed a system that will have applications far beyond what we've discussed to this point. lt's complei:; and while the complexity implies unmatched versatility, it undeniably has its intimidating aspects.
At one level of use, MUS 1 should reduce this intimidation by giving the user an Instrument with a specific (though within certain limits alterable) personality the instant that it's turned on, without having to hassle around with loading any additional programs (success) or variables (well, .. ) Also, these program modules should be written so that they easily interface with future expansions of the system, either hardware or software, so that, when needed, they can be accessed by programs offering distinctly different personalities (success here maybe- only tiim will really tel!).
While we've reduced the intimidation, we've not eliminated it entirely because even when using MUS 1 as a stand-alone personality there are some variables which must be initialized before you begin to play- some Information that the system must have in order to operate properly. This data could be part of the PROM, but not without significantly compromising
v ersatility.
For instance, we•ve mentioned in passing a couple of times the System Control Word-CTRL. This is a single word in the computer's RAM memory at location $0E8. lt is most helpful to visualize CTRL as a collection of eight "switches", each bit representing one switch. To MUS 1, only two of these switches have any signifi.cance- D7, which turns the STGs on and off, and D6, which enables or disableE the dynamic mode option. The rest are reserved.
Every time you power up the system, CTRL must be set so that the desired options are selected- there is no default setting that is part of MUS 1. lf you want dynamic mode (which you should, for now) then bit 7 should be turned on. lf you want STGs, bit 8 must be set.
The 4 possible combinations of these 2 bits then have the following significance:

~
00000000
01000000
10000000
11000000

hex
$00
$40
$80
$CO

action
STGs off; dynamic mode off STGs off; dynamic mode on
STGs on; dynamic mode off
STGs on; dynamic mode on
CTRL is not the only variable which must be initialized manually. There's also:

EXTERNALL ',' INITIAL I ZE[) VAR 1 A8LES

LOC. LABEL | USE
0E8 CTRL | SYSTEM CONTROL WORD
D7 SET TURNS ON
TRANSIENT GENERATORS ()6 SETS D'T'NRMIC MODE
OE9 | ODLY | SETS OUTPUT DELA'T';
IN DYNAMIC MODE $20 RECOMMENDED

0EA OUTS NUMBER OF HARDelARE SUPPORTED CONTROL CHANNELS Al/AILABLE
-- AND TRANSIENT PARAMETERS 08A
088
08C
08D
08E

ATCK
DC"'
SUST
RELS
PEAK

ATTACK RATE
| | DECA"' RATE SUSTA I t-1 LEVEL
RELEASE RATE PEAK l/ALUE -SEE TEXT

RATES: $0i <SLOW) $3f <FAST) LEVEL: $0i <MINIMUM)
$3F <MAXIMUM>
Most of these are easily understood or have been examined in the past, so we transient generators are turned on, we also need to enter the attack, delay, sustain and release parameters that we want produced. These four entries should need little explanation other than the examples which follow shortl.y; their range is from $Ol-$3F, with $01 representing the lowest rate or level and $3F the highest. PEAK- this fifth transient parameter needs a little extra attention. PEAK has only one use; it determines whether the transient produced is going to be percussive (quiekest possible attack and full ADSR segments) or non-percussive. In the non-percussive mode, the glide is on for Jill.. segments of the transient and the Decay and Sustain states of the transient are eliminated entirely.
In fact, there is only one bit in the word PEAK that is changed to select one of these two options- the most significant bit. The remaining seven bits should (for now- until you have a real feel for what's happening) be set to $3F (OOllllll in binaryl If the most significant bit of this word is cleared, you're in percussive mode. If the bit is set (so that PEAK contains $BF
- lOllllll in binary) you are in non-percussive mode.
The differences between the two are great. Assume for a moment that we have set the ADSR parameters at $3F /$04/$20 /$01 respectively (fastest attack/moderated decay/medium sustain/slowest release) and that we are only going to change the PEAK parameter. If PEAK contains $3F(percussive mode), a 'scope display of the transient will lock something like this:

vt won •t go into any great detail. A few points

are worth mentioning, however. | key down | key release
ODLY- this is a number that represents the delay that the QuAsh drivers
will use, when required. For normal
use, a value in the range of $20-$30 is most appropriate.
OUTS- this variable tells the POLY subroutine how many output channels it has to work with, so that notes don't get lost; we talked about this last time. Now we need to notice that when the STGs are asserted we should think of the quAsh channel that is producing the transient
as simply an extension of the channel producing the note. In other words, the two QuAsh channels constitute a single "hardware supported" channel. A single QuAsh represents two such channels. ATCK/DCY/SUST /RELS- When the

r~ figure b

Setting PEAK to $BF (non-percussive) produces this result:

key release
figure c | r~

Because the glide is now on during the entire attack cycle and the Decay and Sustain portion of the transients are eliminated. Straightforward stuff, really.
We need to cover an example of system set-up before we wind up, but first must notice that the effect of having the PEAK parameter are far more far-reaching than we've been able to cover in detail. A quick example:
ADSR parameters set to $10/$04/$20 /$01 and PEAK containing $3F will produce this kind of transient:

key down

figure d | r~

which, when heard, starts out with a non-percussive kind of "swell" with a percussive "pip" added at the last instant before the transition to the Decay and Sustain cycles. This would seem to be a unique and useful transient that isn't produced by traditional ADSRs.
Along the same lines, the TSGs can be considered to be "better'' than our hardware ADSRs in that they ~ finish the Attack cycle before transitioning to the Release state. lf a key is released before its transient has gone all the way to PEAK, the transient immediately switches to the release state. This is frequently called "muting' and it offers the possibility of effective control of espression directly from the AGO keyboard. A SUMMARY. OF SORTS
So, we've gotten our hands on a MUS l PROM and are ready to start doing things. What has tobe done first? Really very
little. | --
First, the System Control Word, Output Delay and number of hardware channels available must be set. For example:
keystrokes O-E-8-DISP | explanation
| sets monitor pointer to $ES-CTRL
C-0-ENT | sets $E8-asserts STGs
| dynamic mode
3-0-ENT 0-2-ENT | sets ODLY value
| sets output channels
| at 2
these entries define the personality cf the instrument as a 2 voice polyphonic synthesizer (notes from channels A & C) with software transient generators (which appear at QuAsh channels B & D) .
31

32

Next, we must set the transient parameters to the desired values: keystrokes
0-B-A-DISP

3-F-ENT

explanation
sets monitor pointcr
to $BA-ATCK
s ets shortes t attack
MIX | OUT
o-4-ENT | sets moderate decay
2-0-ENT | sets moderate sustain | figure e
0-1-ENT | sets slowest release | Oh, yes- I almost forgot. OPTN, like
| | POLY 1. 0, uses the 8700 keyboard to con-
| | trol two important functions. Whlle OPTN
| | is running, touching key 0 of the control
| | keyboard will cause the entire system to
| | be re-initialized. Not the entries that we
| | made manually- those remain unchanged,
| | but all the notes and transients go immed-
iately to zero level.
3-F-ENT | percussive mode
and you may recognize these parameters as being those that we examined in the illustration earlier.
Finally, we simply begin running the program:
keystrokes D-0-0-DISP | explanation

Similarly, touching key ill produces RUN

| sets monitor pointer to beginning of OPTN presto- the program runs

A typical patching configuration that would be consistent with these entries would look something like this:

a tuning function that makes the synthesizer respond as if all the channels were seeing the second C-;;;; a three octave keyboard held down. The transients go, the notes play, etc. After tuning, be sure

~000-
0D03-
0D06-
0D09-
0D0C-0D0E -
001.:1.-
001.4-
0D:l.6-
0D:l.E:-
00:l.A-0D:l.C-0C.tl.F-

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
2:1. 0D
71. 0D
C3 0D
28 0D
BF
20 08
00 0F
01.
EE:
E9
5C
52 0D
E2

. :t: +·+' ;t::t. :+· * :t; .f: * :t: :f, :i: :t: :t: :f: :+: * :+: :f: :t::t: :t: :f: :t: :t: :i·::f; :t::t: :t: :+:
* | * ·~ | MU:'.J | .+• •i: | 1
::+. | E::'T' .J(JHt·J SlMC.lt·nUt·~ | +·
: •+•O::C | 1.9?:c: F'HIA ELECTRONIC'.c'., | HK:+•
:* | ALL RIGHTS RESERVED | *
·* | * : :t:
: :t: | S'T'NTl-IES l ZE~: '.::;UBF.:1)UT 1 NES | .+:
:* | ++ AND ++
:ot• | t1UL TI PLE CIPT I or• PCJL','F'HON l C | •t•
: * | ALLOCAT I Ol·l PF~OGRAt1 ~·H TH | *
: * | '.';.OFHJARE TRRr•SIHff | * : •+• | GENEF.:fH 1 ON | •+•

;:+:
,******************************** OPTt·l
: P•JL '.'PHOtH C S','tHHES I ZEF: / OPTI ON SELECTIOt·l
=********************************

INIT . DL €1D2:l.
POLY . DL 0C•7:l.
TRGN . DL 0DC3
NOTE . DL 0D2B
DECD . DL 0F00
FILL . DL 0D52
DISP . DL 0820
CLCK . DL 00BF

:OPTION TIES MUS:!. FIRMWARE :TOGETHEF: INTO A POL'T'PHC!tHC S'T'tHH : WITH OR WITHOLIT TRANSIENT GENER-: TI ot~; W/l•lO DYNAM I C IJUASH DRIVERS

:ALSO USES PIE8UG DECODE AND
: ASSIGNS KE',' #0 AS S','STEt1 CLEAR :AND lt:l. AS TUNE - EQUIVALENT TO : ALL CHANNELS 21m "c" ON fc~BD DOW~
OPTN .JSF~ ItHT | :ZERO ALL BLIFFS
LOOP JSR POL'T' | :ALLOCATE CHANS
JSR TF:GN | : NE•l TRANSIEtHS
JSR NOTE | : OUTPUT-F.:EAD ftGO
U>A ·~CLCK | :GET CLOCK VALUE
STA [:•ISP | : F.:AZZ-MA-TAZZ
JSF.: DECD | :CHECK COMMANDS
Ct1P 01. | : ~:::1? | :1? | >:!.?
8MI OPHl | :0; CLEAF.: ALL
BNE LOOP | ::>:!.; KEEP ON
LD¹
T1 | 5C | ::!..• TUN!': 2ND c JSR FILL | : KE'r'S ALL C"JWN
BEQ LOOF' | : 8F.:AtKH ALi·JA'T'S

ItHT
INITIAL!ZATIOt• ROUTINE
:********************************

CTRL . DL 0€1EE:
TBEG . DL 00BF

0D2:l.-
0D23-
0D25-
0D26-
0D28-
.E!D29-

ß[:•2E:-
l1C•2[:•-
f1C12FüDJ:(.1-
m:·::;2--
f1D35-

~3D:::::-
üD::::~A-
[1C•3:C-
[1D3:E-OC-4(1-
üD42-
0D44-
0D46-
0D47-
"1[:049-

A9 00
A2 28
D8
95 BF
CA
D0 FB

A2 :10

### 85 CF

1.8
7!:i BF
::;[:• üü
9D EF

J:~j (1F
~::19 80 24 E:C:

5~Z1 134
D5 R9
F0 05
A4 E9
::;:::;;
[.H::.'I FD
95 A9

~39
~39

to re-initialize the system by touching control key # 0.
I prefaced one of the earlier paragraphs with "at one level of use. " In all of the preceding words, that's all that we've examined- one level of use (the simplest and most obvious level, at that.) . I've also referred in the past to "software modules" which can be strung together in different ways (just as can hardware modules) to produce different effects and personalities. MUS 1 is the first set of these modules.
With more regret than you can imagine, I haven't the space here to go into all of the implications of this (even if I knew them all, which l'm sure I don't). Providing you're more than just cas -ually interested, you should spend some time trying to understand how MUS 1 works internally (there are numerous different entry points to the routines that we haven 't covered - for instance). I believe that the time investment will be wisely made.

:INIT CLEARS INPUT BUFFER (KTBL)
: OUTPUT BUFFER ( tHBL) ANO TRANS-: POSE 8UFFER/CONTROL •JORDS (TTBL) : HEXADECit1AL MO[>E IS SELECTED

:ENTER AT INT0 TO FILL TABLES
: WITH CHAF.:ACTER FROM ACCUMULATOR
INIT LDA 00 | :PREPARE TO ZERO
INT0 LDX 28 | :SET POINT/COUNT
CLD | :SET HEX MODE
INT:l. STA >1<TBEG, X :ZERO BUFFER
DEX | :ROINT TO NEXT
BNE INT:l. | : SOt1E LEFT -LOOP

NOTEOUT/LOOK
::l.6 CHANNl;:L QUASH DRIVERS AND AGO KEYBOARD READING ROUTINE
:********************************
CTRL | DL 00EE:
ODLY | DL 00E9
KT8L | DL 00DF
NTBL | DL 00CF
TTBL | DL 00BF | :ALSO CLCK
LAST | DL 00A9
:':/H | DL f1:;.EF
l:• . ..-'H | DL (19(10
KE:C• | [:•L ü8l.ü
*** t-.ICITEOUT *** UT't·JAM 1 c OUASH DI':'. I \·'E~'.S

. CiET:O: NOTES TO BE PLA'T'ED FFWM THE :OUTPUT E:UFFER (NTBL) AND ADDS
: TRAt·lSPOS ING './AL.UE FF.:OM TRANSPOSE
. E:UFFEF.: ( TTBL>. | OUTPUTS RESUL T
t·K!TE LD:": 1.0 | :SET POINTER
NOü | LC•A *tHE:L, ,·'· :GET NOTE
C:LC | :PREPAF.:E AN['
A[:•C •t•TTBL.. ~< | : ADC• TF.:ANSF'OSE
s:TA [:•/A | :LET [),.-·'A SETTLE
STA S/H | ::~: | : 1•F:ITE TO S/H

. t<Ol·J THE [>','NAM I C PAF.:T; I F GL IDE
- 1 5 ON .. C'ELA',' I S SKI PPE[:•. I F NOTE
- E; SAME AS L.A~'.T PLA'.'ED <IGNOF.:ING :COtHF.:üL BITS [>6 .!:O, D;>;. [>ELAY IS
: 5K I PPE[). I F NOT IN [NNAM 1 C MODE : Arm NO GL IDE, [>ELA'T' AL•JA','S TAKEN
8t'1I N02 | :GLIDE? NO DELAY
O~:A 8C1 | · IGNOF:E FLAGS
BIT :+:CTF.~L | : D"r"NAMIC MODE ~,
B'v'C [)LA'T1 | NO .• JMP TO DELAY
CMP *LAST.•~< | COMPARE TO LAST
BEC:! N02 | SAME:SKIF' DELA','
DLA'T' L[:o',' =t:ODL'T¹ | GET [>ELA'T' VALUE NO:l. | DE ¹
T 1 | C>ECF.:EMENT DELA'T' E:NE NO:l. | LOOP TIL DONE
t·~O~:.:: | 5TA ·~LAST.·:,, | FOR NE~n TIME

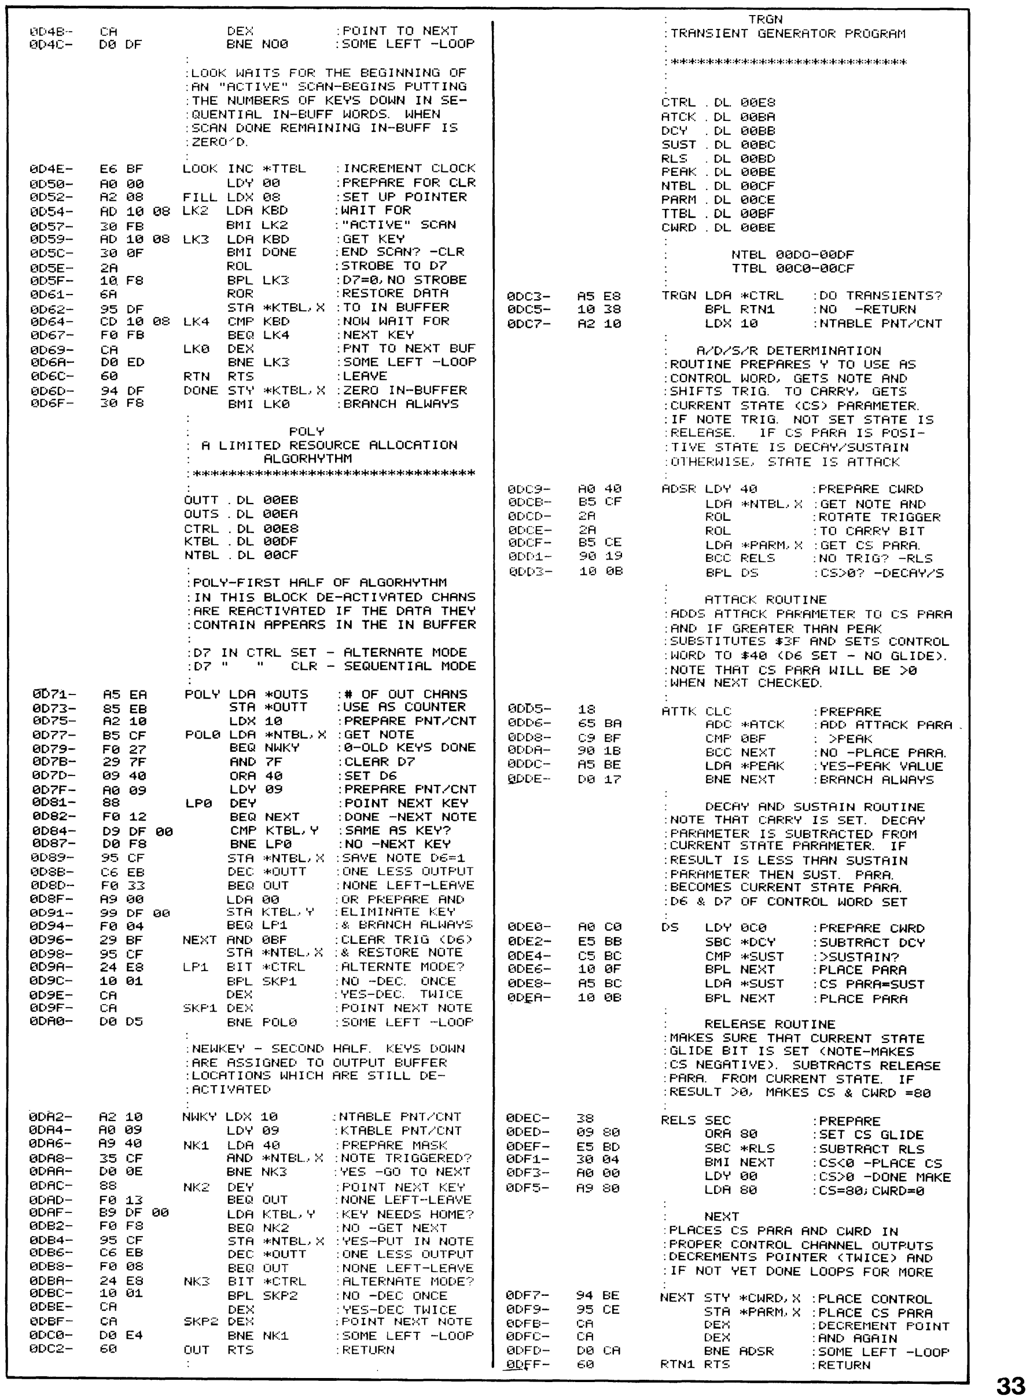
[picture p19: page 5]

OD4E:--
0{)4C-

0D4E-
~lD50-
0D52-
t:1l•54-
0[:057-
(1059-
0D5C-0D5E-0D5F-0D61.-
0D62-
0D64-
0D67-
0D69-
0D6A-0C•6C-0D6D-0D6F -

0D7:!.-
0D73-
0D7S-0D77-
0D79-
0D7B-0D7D-0D7F-0D8:1.-
0D82-
0D84-
0D87-
0D89-
0[>8B-0D8D-0D8F -
0D9:1.-
0D94-
0D96-
0D98-
(1D9A-0D9C-0D9E-0D9F-0DA0-

0DA2-
0DA4-
0DA6-
0DA8-
0DAA-0[>AC-0DAD-
0DAF - 0[)82-

0DB4-
üDB6-
0DB8-
0DBA-0DBC-0DBE-
Q[)6F-0t:•C0-
0DC2-

CA
D0 DF

E6 BF
AC1 00 A2 08

RD :1.0
3:0 FB

DEt-:
BNE N00

:POINT TO NEXT :SOME LEFT -LOOP

: LOOK 1.oJAITS FOF~ THE BEG INNING OF : AN "ACTI VE" ~:CAN-E•EG INS PUTT HlG : THE NUMBERS OF KEYS DOwt; IN SE-:IWENTIAL IN-BLIFF WlRDS. fJHEN
: SCAN [>OUE REMAHHt·m IN-BUFF IS :ZERO··"[).

LOOK I NC *TTE:L
L[>'T' 00
FILL LDX 0~:
08 LK2 LDA KBD

AD :1.0 08 LKJ;
30 0F
| BMI LK2 LDA KBD E:MI t:•ONE
| ROL

ItKREMEtH CLOCK
:PREPARE FOR CLR
: SET UP POHHER : WAIT FOR

:"ACTIVE" SCAN
:GET l<EY :END SCAN? -CLR

:STROBE TO D?
:D7=0,NO STROBE
:RESTORE DATA
:TO IN BUFFER
:NOW WAIT FOR

2A
:1.0. F8
6A
9S DF

BPL LK3 ROR

CD :10 08 LK4
F0 FB

STA *KTBL.. X
CMP KBD
| | BEO LK4 | : NEXT K:EY
CA | LK0 | ['E~: | :PNT TO NEXT BUF
| | | :SOME LEFT -LOOP
| | | :LEAVE
D0 ED | | BNE LK3
60 | RTt; | RTS
94 DF 30 F8

AS EA
85 EB A2 :1.0

BS CF
F0 27 29 ?F

09 40
A0 09 88

F0 :1.2
D9 DF 00 D0 F8

### 95 CF

C6 EB F0 3J:

A9 ~30

### 99 DF 00

F0 04
29 BF

### 95 CF

24 E8
:1.0 0:1.
CA
CA
D0 D5

A2 :1.0 A0 09

A9 40
J:5 CF D0 OE
se
F0 :13 89 C>F 00
F0 F8

### 95 CF C6 EB

F0 08
24 E8 :10 0:1.
CA
CA
D0 E4
60

DONE ST'T' *KTBL .. X
BMI LK0

POLY

:ZERO IN-BUFFER
:BRANCH ALWAYS

A LIMITED RESOURCE ALLOCATION ALGORHYTHM
:********************************

OUTT . DL 00EB
OUTS . DL 00EA
CTRL . DL 00E8 KTBL . DL 00DF

NTBL . DL 00CF

:POLY-FIRST HALF OF ALGORHYTHM :IN THIS BLOCK DE-RCTIVRTED CHANS :ARE REACTIVATED IF THE DATA THEY :CONTRIN APPERRS IN THE IN BUFFER

: D7 IN CTRL SET - ALTERNATE MODE
: D7 " | CLR - SEQUENTIRL MODE

POL~· LDA *OUTS STA >t<OUTT

LDX :1.0 POL0 LDA +NTBL, ~:

BEQ NWKY
AND 7F
ORA 40
LDY 09
LP0 DEY
BEQ NEXT
CMP KTBL,Y
BNE LP0
STA =t:NTBL~ :=<
DEC >t<OUTT
BEO OUT
LDA 00 STA KTE:L. '."
BEO LP1
NE)<T AND 0BF STA *NTBL~ ~<

LP1 8 IT *CTF:L
BPL SKP1 [)E::<

Sk.F'1. DE>=:
8NE F'OL~21

: NEl.oJKE'T' - SECOND
: AF~E ASS I Gt·lED TO
:LOCATIONS WHICH
: ACT 1 VATE[:•

NfJK~' L[>X 10
LD ¹
T1 | 09
NK:I. | U>A 40 AND >1<NTBL..· ~:

BNE t<K3

:# OF OUT CHANS :USE AS COUNTER

:PREPARE PNT,.'CNT
:GET NOTE : 0-0LD KEYS [>ONE

:CLEAR D?
:SET D6 :PREPARE PNT/CNT

:POINT NEXT KEY
:DONE -NEXT NOTE
:SAME AS KEY? :NO -NEXT KEY

:SAVE NOTE 06=1.
: Ot;E LESS OUTF'UT
:NONE LEFT-LEAVE
: OF; Pf':EPAPE At-W
: ELIMitlATE KE'." : .i, 8F;ANCH AU~A',O;o:

:CLEAR TRlG (D6:>
.& RESTORE NOTE
. AL TERNTE MODE'C.•
: Nü -DEC. ONC.E : 'T'ES-OEC. T\,J ICE

:POINT NEXT NOTE
: 50ME LE:.FT --LOOP

HALF. f<EYS DOi.JN
OUTPUT BUFFER AF:E STILL [>E-

: tHABLE Ptfl ,.·'UH
:KTABLE PNT/CNT
: F'F:EPARE MASf•:: NOTE TRI GGEF:EDC.·

: 'T'ES -GO TO NEXT
DE'r'
BEQ | : POINT NE)-:;T f':E','
OUT | NONE LEFT-·LEA'./E

NK3

5KP2

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
DE:":
DE~·:
BNE
F'.TS
KTE:L, V | : KE'" NEEDS HOl1E? NK2 | :MJ -GET NEXT *NTBL~ >:: : 1

T'ES-PUT IN t·~OTE
*OUTT
OUT
••CTRL
SKP2

NK1

:ONE LESS OUTPUT
NONE LEFT-LEA\"E : AL TEF:NATE MODE",''

:NO -DEC ONCE
','ES-DEC nn CE : POINT NE~<T t-.IOTE

·SOl1E LEFT -LOOP
: F:ETUF:N

0DC3-
0DC5-
0DC7-

0L:•C9-
üDCB--
(1DCD-
(1[:•CE - 0DCF-

~3DD1.-
0[.•(:oJ:-

(1[)to5-
(1[:•[•6-
CIDD8-
0[:•[:•A-0DC1C-
'1DC•E-·

0DE0-
(1[:•E2-
(1DE4-
0DE6-
0[.„E8-
0Df:A-

0DEC-0DED-ODEF-ODF:lt1DFJ:-
0DF5-

0DF7-
0[>F 9-
e:1C>FE1-
0DFC-
(1[:.FD-
.Q!;>fF-

AS E8 :1.0 38

A2 1.0

A0 4€1

### 85 CF

2R
2A

### 85 CE

9ü :19
:1(1 0B

18

### 65 BA

C9 BF 9(1 :18

A5 BE
00 :17'

A0 C0
E5 BE:
C5 BC
1(1 0F
A5 BC
:10 (18

3:8
t39 E:(1
E5 BD
3(1 04
A0 00
A9 80

94 BE
95 CE
CA
C.A
DIZ1 CA
60

TRGN
: TRANSIENT GENEF:ATOR PROGRAM

: ******************:-1-::f:;f;:f::t::+::+::+::f.

CTF.:L
ATCK
DCY
SUST
PLS
PEAK
tHBL
PARM
TTBL
CWRD

. DL. f10E8
. DL (108A
[>L (10BB
. DL 00BC
DL 0(1BD
. DL 00BE
DL 00CF
. DL 00CE
. DL 008F . DL 00BE

NTBL 00D0-00DF
TTBL 00C0-00CF

TRGN LDA >1<CTRL
BPL F:TN:I.
LDX :1.0

:DO TRANSIENTS?
:NO -PETURN
: tHABLE PNT/CNT

A,·'[>,.'S/R DETERMINATION :ROUTINE PREPARES Y TO USE AS :CONTROL WORD, GETS NOTE AND : SHIFTS TF:IG. TO CARR',0, GETS

: CURF:EtH STATE <CS) PARAMETER. : I F NOTE TRI G. NOT SET STATE I S :RELEAS~ IF C.5 PARA IS POSI-

TIVE STATE:. 15 DECAY/SUSTAIN cn·HERWISE, STAlE IS ATTACK

AC•"·F: LD',' 40 | . PREPARE CWRD
U>A :HHBL, :•: : GET NOTE FIND ROL | :ROTATE TRIGGER
F:OL | : TO CAF:F:',' BIT
LDA :t:PAFö~M .. ~< | : GET CS PARA.
BCC RELS | :NO TRIG? -RLS
E:F'L DS | : CS:>0? -DECA'T'/S

ATTACK ROUT!t<E
. AD[>S ATTACK PAPAMETEF: TO es PAF.:A : mm IF GPEATEF: THAN PEAK : SUBSTITUTES oC:F AN[:> SETS CONTROL

: ~·JüR[> TO $40 ( D6 SET - NO GL IDE). : NOTE THAT CS PARA ~H LL BE >0 : ~~HEN NE)O' CHECKED.

ATTK CLC
ADC :t:ATCI<
C11P OBF
8CC NEXT
LDA *PEAK Bt;E NE)'.T

: PREPA~:E
:ADD ATTACK PARA
: >PEAK
: NO -PLACE PARA. : ','ES-PEAK VALUE

:BRANCH ALWAYS
DECR',' Ar-m SUSTA rr; ROUTINE : NOTE THAT CAPRY I S SET. DECAY

: PA~:AMETER 1 S SUBTF;ACTED FF:OM : CUF:RENT STATE PARAMETER. IF

:PESULT IS LESS THAN SUSTAIN : PAF;RMETER THEN SUST. PARA. : BECOl1ES CURRENT STATE PARA.

: [>E: & D? OF CONTROL •JORD SET [>S LD~' OC0
SBC *DC~'
CMP >1<SUST BPL NEXT

U>A *SUST
BF'L NEXT

: PREPAF:E CWRD
:SUBTRACT DCY
::>SUSTAIN?
:PLACE PARA
:CS PARA=SUST
:PLACE PARA
RELEASE ROUT !NE
:MAKES SURE THAT CURRENT STATE :GLIDE BIT IS SET <NOTE-MAKES

: CS NEGAT I 'IE). SUBTRRCTS RELEASE : PARA. FROM CURRENT STATE. I F :RESULT >O, MAKES es & CWRD =80

RELS SEC
ORA 80
SBC >t=F~LS
BMI NEXT
LDY 00
U>A 80

NEXT

:PREPARE
: SET CS GLI DE
:SUBTRACT RLS
:CS<0 -PLACE CS
:CS)-0 -DONE MAKE
.CS=80;CWRD=0

PLACES es PARA AND CWRD IN :PROPER CONTROL CHANNEL OUTPUTS : [>ECREMENTS POINTER <TWICE) AND

:IF NOT YET DONE LOOPS FOR MORE

NEXT STY *CWF:D, X
STA *PARM .. X [)E;><;
l>EX
BNE ADSR PTN:I. PTS

PLACE CONTROL
PLACE CS PARA DEC~:EMENT f'O I NT AND AGAIN

SOME LEFT -LOOP RETURN
33

AFTERTHOUGHTS .....

lt has been pointed out that some perhaps pertinent details have been omi tted from the preceeding explanation of MUS 1.
The most prominent example is "why would you ever want to not have dynamic mode". The most probable reason is for special effects.
In general, the difference between special effects and noise is imagi nation. Contemporary musical lore is full of instances where a special effect resulted from an unsuccessful attempt to do something entirely different. Phil Spector• s original "flanging'' effect, so popular today, was supposed to be voice doubling, but didn' t work.
In this same manner, there will be those who will be able to use the "step glissando" that results from too short a QuASH settling delay as a valid musical device,
Also, the dynamic mode :requires an additional 16 byte tahle area that might easily be put to better use in some programs.
This same philosophy of maximizing versatility is responsible for the QuASH settling delay being an externally initialized variable. For the purpose of effect, there may be times when you want a short delay.
In addition to this, we have seen systems which were marginal in their power supply complement which would have a discernible pitch "blip" when keys were pressed with long delays ( in the $30 - $40 range) - caused by the relatively heavy charging current producing a momentary dip in supply voltage. In these systems, a short term solution has been to decrease the QuASH driver delay to something on the order of $10, The long term solution is more power.

SEVERAL POINTS RELATIVE TO THE OPERATION OF THE STGs SHOULD BE MENTIONED,

Assume that we have set the STG parameters as follows:
ATCK - 08
DCY | 04
SUST | 20
RELS | 04
PEAK - 3F
or in our more or less standard notation, $08/$04/$20/$04/$3F,
If we were able to disahle glide entirely, and then scope'd the transient we•d see this:

figure (a)
1

V
T

as the STG program counted up to the peak and then down to the sustain level before counting down to the base level when the key was released.
If we then enabled the glide and set them to a slightly advanced position and examined the same output we would find that thls change had taken place.

figure (b)
t

V
T

QuASH GLIDE CONTROLS, The setting of the QuASH glide pots have an effect on

The integrating action of the glide circuitry has smoothed the steps of the Attack, Decay and Release, with the exception of the last Attack step where ( as we have already stated ) the glide is off under all percussive circumstances. In this specific case, the last glide-less increment will be hardly noticeable.
If, on the other hand, the glide is set to a long value ( fully advanced, for instance) an examination of the waveform will show this:

the transients produced. In most cases, these controls will need to be advanced only slightly from their fully counterclockwise "off11 position.
The most noticeahle effect of different settings of the glides will be observed when the STGs are set to the percussive mode by PEAK.
When the most significant bit of PEAK is cleared, it will effect only on the last increment of the attack cycle. For all increments other than the last, the glide will be set. A detailed example will best illustrate this.

figure (c)
i

V
T

The heavy glide has slowed the waveform to the point that when the glide-less final increment comes it takes a much greater step ( one that is completely noticeahle, and unique ). The heavy glide also has the effect of slowing the decay and release rates as shown.
lt would also be appropriate to mention at this point that the instantaneous steps produced by the STG/QuASH combination is much faster than the maximum attack rate available from a 4740, or in fact from most ADSRs. Whereas a typical ADSR may have a minimum attack time of more or less 5 milliseconds, the QuASH in dynamic mode can step in a fraetion of a millisecond.
This means that if there are any tendencies on the part of the VCA being used to have interaction between control and signal channels it will be aggravated when using STGs. We may hear "pops" and "thumps" that were not obj ectionable before, Probahly the best solution here is to limit the response of the control voltage inputs of the VCA. In a 4710 Balanced Modulator, this means the addition of a small capacitor. Like this:

Optional
O. 01 typical | 1 ' 1 1
Cl | r----1 ,-----j .TIOll (ö) t·2 Rl | 1 | R4 | 1

MODULA~ l-"J'4\/7K\r-1i,___~v'v'"'\K, __ -.;
R

J2

J3

figure (d)

Another point to be considered is the fact that the output voltage from a QuASH channel doesn•t go to zero - there may be some leakage from the VCA when it is supposed to be off. The easiest fix here is to re-adjust the Modulation rejection control of the VCA being used. In the 4710 this is R25. Be aware that this also limits somewhat the useahle range of the D / A' s TUNE control since wide variations in the setting of this control will affect the leakage from the VCA. Tuning changes on the order of 1/ 4 octave should not present any particular difficulties.
There is a point dealing with this which may not be immediately exploitable by many, but which should be mentioned in any case; the action of the trigger outputs of the QuASH channels which are being used as STG channels. The trigger outputs QuASH channels which are being used to produce pitch setting voltages behave in the normal manner. When the AGO key

.....----llo1J----L
In

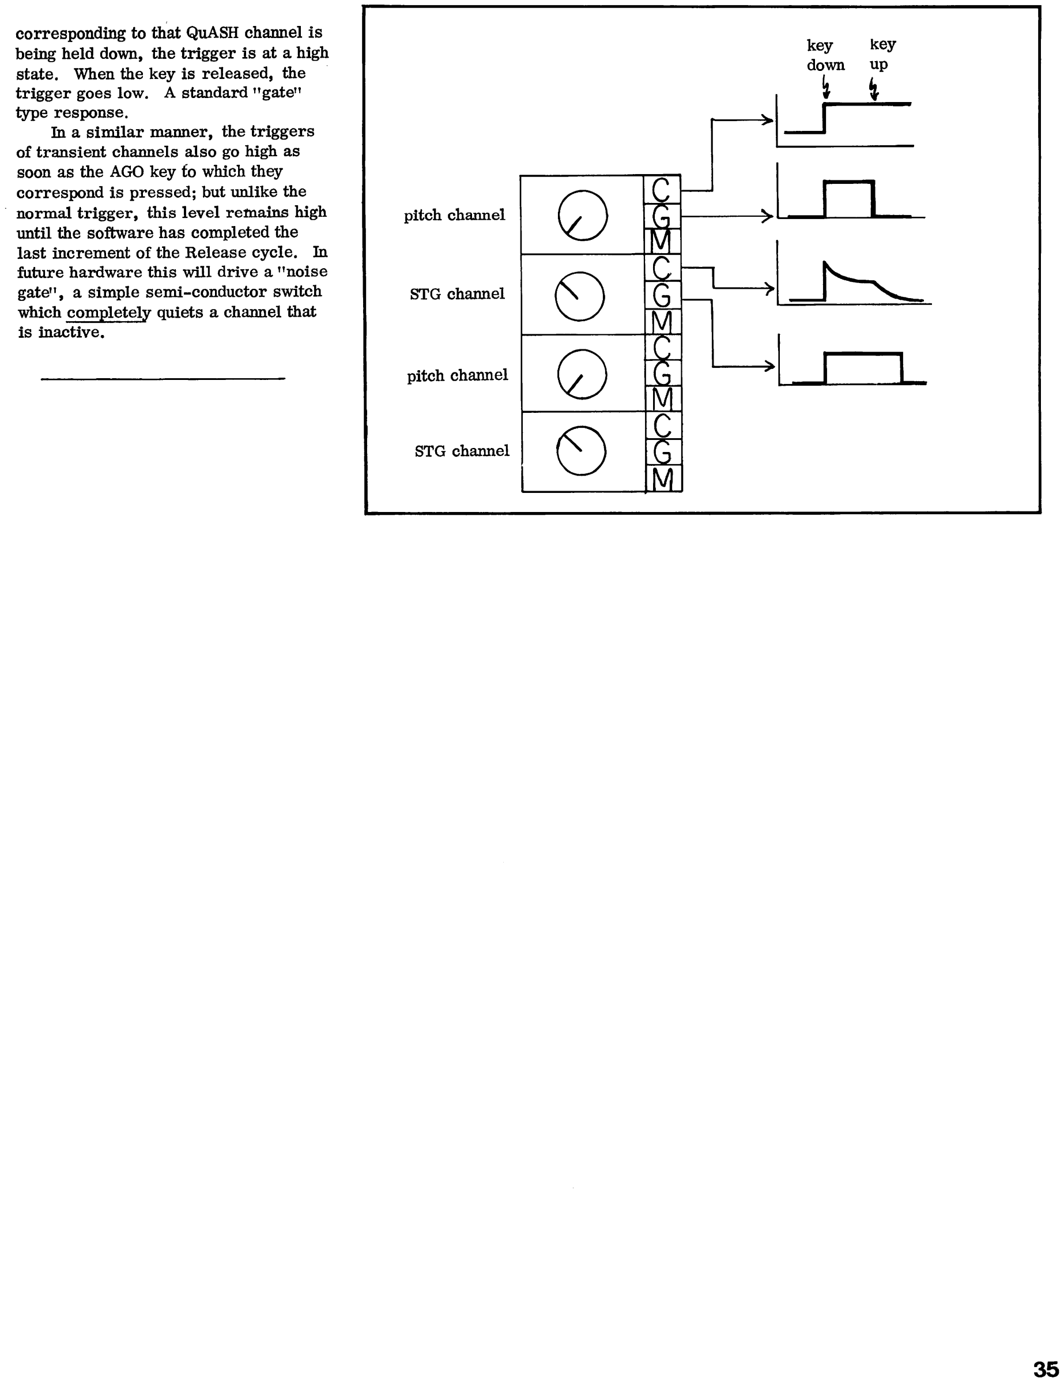
[picture p20: page 7]

corresponding to that QuASH channel is being held down, the trtgger is at a high state. When the key is released, the trigger goes low. A standard "gate" type response.
In a similar manner, the triggere of transient channels also go high as soon as the AGO key to which they correspond is pressed; but unlike the normal trigger, this level re:ina.ins high until the software has completed the last increment of the Release cycle. In futu.re hardware this will drive a "noise gate", a simple semi-conductor switch which completely quiets a channel that is inactive.

pitch channel

STG challnel

pitch channel

STG channel

key | key
down | up

L
