Skidlz/PAiA-8700/Tape Programs/O-Glide/O-Glide.pdf

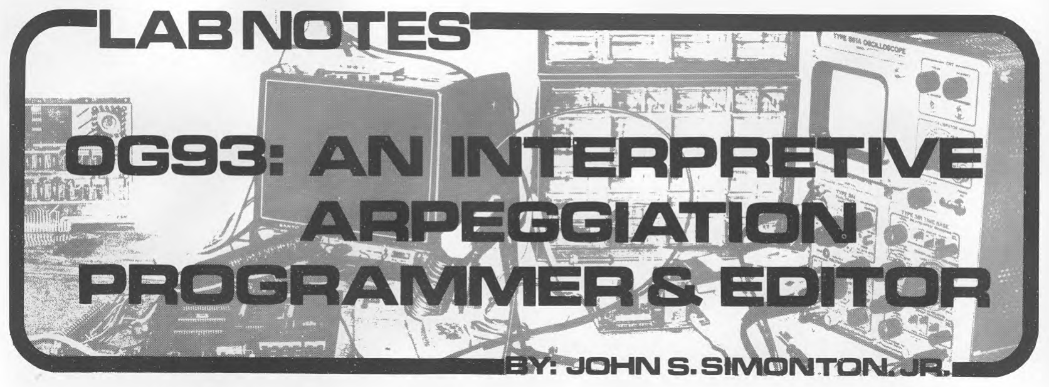
[picture p21: figure]

One | of | the | major advantages that
our hybrid | computer/synthesiser | system
offers is the ability to realize a class of new tricks which for lack of a better
term we'll | call "keyboard effects". | I
have in mind new sounds which arise | not
so | much | from | the timbre of each note,
but from | the | timing | and | sequence | in
which | the | keys played are converted to
notes | and | how | they're | allocated | to
available output channels.w
Using | this | definition, | I suppose
that POLY-SPLIT | from | last | time | would
qualify | as a keyboard effect because it
affects the way that keys held down | are
allocated | to | note-producing | output
channels. | But, ECHO (January-March 1979
Polyphony, page 29) is | more | specificly
what I feel the term should mean because
with | that | program | new effects (and at
short delay settings, new timbres) arise
that would | be | extremely | difficult | to
accomplish | without | some | means | of
juggling key activations and how they're assigned to outputs.
Another good example would | be | the
ORGASMATRONIC | GLIDE | arpeggiation trick
that the keyboard encoder and D/A did by
themselves | (remember?). | Hold | down | a
bunch | of | keys | and | the encoder, while
scanning, stopped | momentarily | when | it
reached | one of the down keys and played
the note briefly before | continuing | the
scan. | When another key was found down,
it stopped again to play that | one, | and
so on. | Altogether an alright thing that
allowed | arpeggiations to be played much
more rapidly than they could be | without
electronic assistance.
When | we | installed the computer in
the loop, we | lost | Orgasmatronic | Glide
(06), | which | maybe | was not such a huge
sacrifice | when | considering | the | power
that | was | gained | in | the | process; but
still, I know several folks who | mourned
the | loss | because it was an effect that
they were using to good purpose in their music.
Here's a terrific replacement. This new program does the same thing that the
old OG did, hold down a | bunch | of | keys
and | it | plays | them in sequence, but it
also gives control that wasn't | possible
with | the | old | "state machine" version.
For | instance, | it | can | arpeggiate
down-scale | as well as up. | And it plays
staccato | or | legato. | It | also | allows
touch | pad | control of glide and similar
control | of | the | tempo | of | the
arpeggiation.
Great. But not the greatest part, we'll get to that soon.
Enter the program | as | outlined | at
the | end | of | the | column | and | start it
running, then | press | down | a | group | of
keys. | If | you've | done | everything
correctly, you should hear a | relatively
slow | down-scale | arpeggiation | of | the
notes that you're | holding | down. | When
the lowest note has played, the sequence should start again from the highest.
Now | let's | play | with | the control
some. | Here's what the | keys | mean | with
OG93 running:

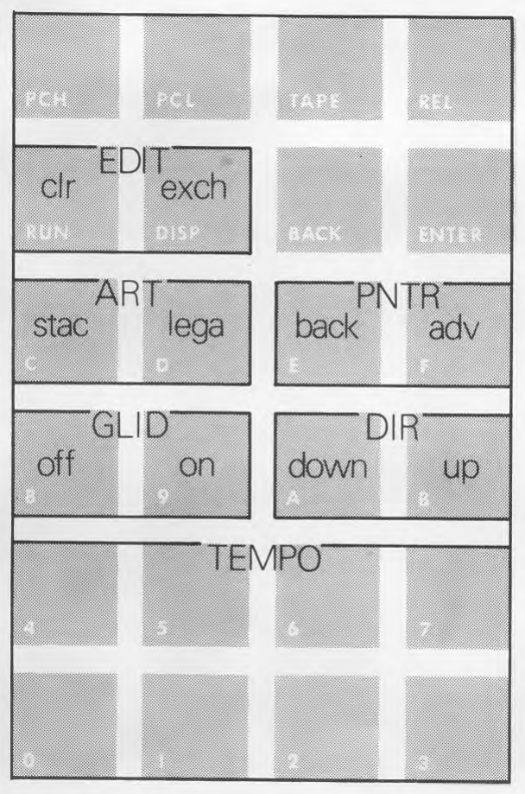
[picture p22: figure]

Touching | the DIR:UP pad will cause
the | arpeggiation | to | change | direction
from | down-scale | to | up. | GLID:ON turns
the glide for the | arpeggiation | channel
on | and | (you guessed it) GLID:OFF turns
it off.
The LEGATO ARTICULATION pad | causes
the | trigger | signal | to | remain high as
long as any keys are down so that | there
will | be | no re-articulation as one note
finishes playing and | the | next | begins.
STACCATO | ARTICULATION triggers the note
the first instant | that | it | plays | then
releases the trigger.
The | TEMPO | keys | cause the rate of
arpeggiation to change from slow (7) | to
fast | (0) over a range from so slow that
almost | anyone | could | play | the | run
manually | to | a rate that's so fast that
the | sequence | begins | to | take | on | the
texture | of | a | chord (which should give
you | a | clue | to | one | interesting
application | of | OG93 | in | a | piece | of
music).
If you were an | Orgamatronic | Glide
fan | in | the | first | place, | we | could
probably | stop | here | and | you'd | be
completely | happy - the program is a lot
better | than | the | old | manual | version.
We'd | also | be stopping before we really
got started, because | by | far | the | most
interesting feature of OG93 is that it's an interpreter that allows us to program a series of arpeggiations and an editor that makes the entry and manipulation of those programs easier.
Each program step contains | all | of
the | information | that | we | controlled
earlier (glide on and off, | up-scale | or
down, | staccato | or legato, and one of 8
tempos) and when | the | program | is | run,
each | step | will be taken in turn and an
arpeggiation | of | the | keys | held | down
performed | using | the | status | of | the
parameters specified by that | step. | At
the | end of the program it jumps back to
its | beginning | and | the | sequence | of
arpeggiations repeats.
Each | step | of | the | program | is
"written" in exactly the same | way | that
we | set the parameters earlier; in fact,
as you'll | soon | realize, | you | were | in
effect writing the first step then. | The
key to forming these steps into programs
is | the PNTR : BACK/ADV block of pads on
the | command | keyboard. | The | pointer
(PNTR) | refers | to the program step that
you're writing.
One quick example | should | get | the
idea | across. We'll write a program that
sweeps up the | keyboard | at | a moderate
tempo, | re-articulating | each | note,
followed | by | a | quick | legato | run
down-scale. | Program | the first step by
touching these keys - | TEMPO:4, | DIR:UP,
GLID:0FF, | ART:STAC. | That takes care of
the up part.
Now for the | down | part, | begin | by
touching | PNTR:ADV | so the commands that
we | enter | next | are | "pointed" | at | the
second program step (which is step #1 as shown in the displays, the first step is
#0) | and | touch | TEMPO:2, | DIR:DOWN,

GLID’.OFF, ART:STAC. | Now hold down a big
chord structure to hear the full | effect
of this dual arpeggiation.
30 | POWHONy | November/December 1979

Editing | an | existing | program | is
simply a | matter | of | pointing | to | the
program step that you want to change and
entering | the | changed | parameter. | To
change | the | first | step | (#0) | in | the
example | above | to | a | slower tempo, for
example, touch PNTR:BACK so the | display
shows | 00 | and | then | touch | TEMPO:7 (or
whatever).
0693 can handle programs | up | to | 8
arpeggiations | deep | and, when you begin
stacking that many steps, it's | easy | to
get | lost. | The EDIT:EXCH key helps here
by | allowing | us | to | remove | the | step
pointed | to | from | the | program | and
replacing it | with | an | instruction | for
repeat. | By | backspacing the pointer to
step #1 and touching the EDIT:EXCH | pad,
we | cut | the | program | to just the first
step, EDITlEXCH again and | the | original
program | step | is back in place, so that
the | entire | program | runs | again. | By
stepping through the program and causing
it | to | repeat | after the 2nd, 3rd, etc.
steps, it's fairly easy to locate | where
in | the | program | a | specific | sound | is
coming from and then make changes there.
As you may surmise from | the | name,
the | EDIT:EXCH | key | causes | the program
step pointed to to be exchanged | with | a
memory | buffer | location | which | is
initialized to contain the interpreter's repeat code (00). This implies that this
key can also be | used | to | exchange | two
program | steps | by pointing first to one
and touching EDIT:EXCH and then | to | the
next and again EDIT:EXCH. | In fact, this
is | the | case; | with one exception. | The
first step of the program may not be the
repeat | code | 00. | If | it | is, | the
interpreter will lock up as it reads the first step, finds that it's a repeat, so
it | reads | the | first | step, | and so on.
0693 protects against this | by | checking
to | see if you are pointing to the first
program step and, if you | are, | checking
to | see | if you're getting ready to make
it 00. | If you are, it doesn't | complete
the | exchange. | You can get around this
if you want to exchange the | first | step
with | another | by | pointing to the other
step first, EXCHanging, and | then | going
to step #0 and EXCHanging again.
The | final | editing | key | is | CLR
(clear). | Touching this pad | clears | the
program, with the exception of the first
step, | which | remains | unchanged for the
reasons given above.
For | detailed | operational
information | there | is no substitute for
the | liberally | commented | assembler
listing | at | the | end, but let's talk in
general | terms | about | how | the | program
works.
We | use | the | MUSI firmware NOTE to
take care of the dynamics of maintaining
analog outputs that | must | be | refreshed
and | to read the A60 keyboard. | The list
of keys which the | firmware | returns | as
being | held | down | is | the "arpeggiation
list", or the notes to | be | played. | In
simplest | terms, | 0693 | does nothing but
delay | for | a | period | of | time | which
determines | tempo | and, when the time is
up, pulls the next key from the list and
plays it as a note. | The | bulk | of | the
rest | of | the | program checks that we're
not yet to | the | ends | of | tables | (keys
down, | program | steps, | etc.) and, if we
are, takes | car | of | starting | from | the
beginning | again, | and | controls | things
like re-setting the tempo timer when | it
expires | and | re-articulating | between
notes when playing staccato.
Most of the arpeggiation | program's
control | information is contained in the
single | word | of memory | labeled | SCTL
(sequence control) in the listing. The 8 bits of that word have these uses:
DDDD | D
7 6 5 4 | 0

# Illi TEMPO-1

### I L-NOT USED I------ 1= LEGATO ----------1= DIN: UP

When | the | interpreter | needs | the
tempo, it extracts | it | from | this | word
with | an AND operation (statement 1440).
The status of the control bits D6 and D7
are determined with | BIT | operations | at
lines 0790 and 0900.
When | one | run has finished and the
next is due to | begin, | the | interpreter
pulls | the next program step from memory
(the program buffer CSEQ) | and | after | a
manipuation | which | immediately isolates
the glide controlling | bit, | places | the
program | step | in the control word SCTL,
where the rest of the | program | accesses
it | as | outlined | above. | The | isolated
glide bit is | immediately | rotated | into
the | most | significant | bit | of | the
transpose | buffer | (TTBL) | word | corre-
sponding | to | the | ouput | channel | being

# DON LANCASTER’S

# INCREDIBLE SECRET MONEY MACHINE

# A cookbook for creating your own computer or

tech venture.

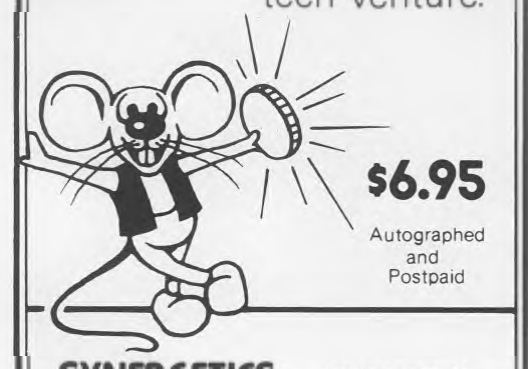
[picture p23: figure]

## SYNERGETICS box 1077 p

THATCHER, AZ 85552

( | ) Send | ISM M's ( > Check ( ) Visa
( | ) Send FREE Lancaster Booklist

Name_______________________________________

Address_____________________________________

City | State | Zip
Exp | / | Signature

0010
0020
0030
0040
0050
0060
0070
0080
0090
0100
0110
0120
0130
0140
* | ORGRSMATRONIC GLIDE | *

*(C) 1979 PAIA ELECTRONICS, INC*

****** MONITOR SUBROUTINES ******

* | ARPEGIATION PROGRAMMER AND | *
* | EDITOR | *
* | BY | *
* | JOHN 5. SIMONTON, JR | *

THIS IS THE MAIN PROGRAM LOOP. START BV INITIALIZING THE SYNTHESIZER AND CALLING THE QUASH DRIVERS AND AGO KBD READING ROUTINES FROM MUSI CHECK TO SEE IF A COMMAND KEV HAS BEEN TOUCHED; AND IF SO, JUMP TO SUBROUTINE TO DETERMINE THE COMMAND Al® EXECUTE IT. DETERMINE THE POINTER FOR THE OUTPUT CHANNEL Al© JUMP TO SUBROUTINE FOR ORG. GLIDE 0590 : PROCESSING. ON RETURN, LOOP.

0690

0540
0550
0560
0570
0580
♦1000LLL | | | 0600 | :
1000- | 20 21 ID | JSR | 0610 | JSR INIT | MUSI SYNTH INIT ROUTINE
1003- | 20 28 ID | JSR | 0620 | LOOP JSR NOTE | QUASH DRIVERS AND READ AGO
1006- | 20 00 IF | JSR | 0630 | JSR DECD | PIEBUG READ COMMAND KBD
1009- | 80 83 | BCS | 0640 | BCS HERE | IF NO NEW KEV TOUCHED, SKIP NEXT
1008- | 20 00 11 | JSR | 0650 | JSR CMND | CALL COMMAND DECODER
100E- | A0 0F | LDY | 0660 | HERE LDY 0F | POINTER TO ORG. GLIDE OUTPUT CHANNEL
1010- | 20 16 10 | JSR | 0670 | JSR STAR | CALL ORG. GLIDE PROGRAM
1013- | 4C 03 10 | JMP | 0680 | JMP LOOP | LOOP TO CONTINUE

FIRST THE TIMER IS TESTED AND IF NOT TIME FOR THE NEXT NOTE PROCESSED THE STACCATO CONTROL BIT IS CHECKED AND IF CLEAR (STACCATO) BRANCH IS TAKEN TO DE-TRIGGER NOTE IN OUTPUT BUFFER. IF LEGATO MODE, EXIT IS IMMEDIATE

0700
0710
0720
0730
0740
1016- | 24 E7 | BIT | 0750 | STAR BIT *KTBL+07
1018- | 50 IE | BVC | 0760 | BVC SINT
101A- | C6 72 | DEC | 0770 | DEC *TIMR
101C- | 30 05 | BMI | 0780 | BMI ADVA
101E- | 24 74 | BIT | 0790 | BIT *SCTL
1020- | 50 46 | BVC | 0800 | BVC CLRN
1022- | 60 | RTS | 0810 | RTS

ARE THERE ANY AGO KEYS DOWN?
NO KEYS, BRANCH TO RE-INIT ARP. POINTER OTHERWISE, DECREMENT THE TIMER

IF EVENT TIME, BRANCH
OTHERWISE CHECK FOR STACCATO AND IF TRUE... BRANCH TO CLEAR TRIGGER FROM OUTPUT NOTE

OTHERWISE, RETURN WITHOUT CLEARING TRIGGER
POUPHONU | November/December 1979 | 31

# REVIEWS

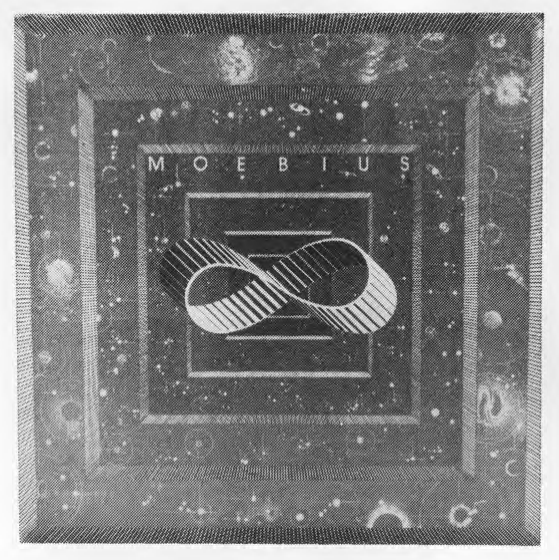
[picture p24: figure]

Moebius
Moonwind Records
MW 33801
This album represents | an | original
foray | into an area which has been dealt
with so often in cliche | that | its | real
possibilities have been largely ignored: pop synthesis. Taking up where Brian Eno and Tangerine Dream left off, "Moebius" combines some of the sonorities of these
groups | with | the | more | minimalistic
production | values | of | groups | like The
Normal and Suicide. Add a dash of biting
lyrics and a mock serious approach, | and
you | have | what | amounts | to the missing
link | between | the | more | traditional
schools | of | pop synthesis and the outer
fringes of new wave. | The | result | is | a
refreshing | LP whose bold approach makes
you wonder why no one has | spotted | this
fertile turf before.
If | "Moebius" | straddles such broad
musical boundaries, it is | in | no | small
part | due | to its personnel, all of whom
are well | grounded | in | synthesis. | They
are: | Douglas | Lynner, editor of Synapse
and former member of LEM, Bryce Robbley,
also of LEM, and | Synapse | correspondent
Steve | Roach. | Their | knowledge | of | the
territory makes for an | album | which | is
not | only | broad in scope, but sonically
inventive using synthesizers, drums | and
violin | as | well | as | effects | such | as
crinkling paper, and processed voices to augment its aural images.
For my money, | the | best | cuts | are
those | which | bear the closest ties with
the | new | wave: | tunes | like | "Light | My
Fire", | where crazed vocals combine with
a bassline gone | bonkers | to | create | an
atmosphere | which | bears | only | a cosmic
resemblance to the original; and | "Clone
Zone", a cut whose cryptic lyrics, naked sequencer and tongue in cheek production
conjure | up | a time when mindless clones
stalk the Earth like giant Xerox | copies
in search of their originals.
Of | the | rest | of the material, the
most accessible cuts are "Urth", and the
title cut which uses sequencers to | good
rhythmic | and | harmonic effect. For more
traditional | tastes, | "Prophecy" | is | a
rolling | instrumental | reminiscent | of
Eno’s dreamier moods.
There | is | a | tendency | towards
overproduction | which | marrs some of the
tunes. It's as if, | in | the | process | of
rejecting | the production cliches of pop
music, Moebius has not yet zeroed in | on
what its own values are. And a couple of
the | tunes | are simply too long. But for
all its flaws, this | is | an | interesting
album | whose | innovative approach proves
that | the | synthesizer | has | far | from
realized its potential in pop.
-Melodie Bryant
32 | POWPHONU

8828
8830 IF IT'S TIME FOR ft NOTE TO BE PROCESSED. THE POINTER TO THE INPUT 8840 BUFFER IS ADVANCED (EITHER FORWARD OR BACKWARD) AND IF THERE IS NO 0858 MORE BUFFER LEFT WE DROP THROUGH TO ADVANCE THE POINTER TO THE SEQUENCE
0860 | BUFFER TO GET THE NEXT SET OF GLIDE PARAMETERS. | IF WE ARE NOT YET
0870 TO THE END OF THE IN BUFFER. WE BRANCH OUT TO RESET THE TIMER. ETC. 0880
1823- | 06 73 | LOX | 0890 | ADVR LDX *PNTR | GET POINTER TO INPUT BUFFER
1025- | 24 74 | BIT | 0900 | BIT *SCTL | CURRENTLY flRPEGGIATING UP?
1027- | 18 85 | BPL | 0910 | BPL DOWN | NO. BRANCH TO DO DOWN
1829- | Oft | DEX | 0920 | DEX | TO GO UP-SCALE. DECREMENT POINTER
1828- | 38 87 | BMI | 0930 | BMI SflDV | IF POINTER NOW <8, BRANCH
1820- | 18 26 | BPL | 8940 | BPL STIM | STILL IN RANGE. BRANCH ALWAYS
182k- | E8 | INX | 8950 | DOWN INX | DOWN-SCALE. INCREMENT POINTER
182k- | E0 08 | CPX | 0968 | CPX 88 | OUT OF RANGE?
1831- | D0 21 | BNE | 0970 | BNE STIM | STILL IN RANGE. BRANCH
| | | 0988
0990 IF WE GET HERE (SADV) IT MEANS THRT WE HAVE PLAYED ALL OF THE KEYS 1000 THAT WERE DOWN AND HAVE REACHED THE END OF THE INPUT BUFFER
1010 NOW IT'S TIME TO GET THE NEXT ENTRY FROM THE CONTROL SEQUENCE. 1020 WE TEST TO SEE IF WE ARE AT THE END OF THE SEQUENCE AND IF SO TI£ 1030 POINTER IS RE-INITIALIZED. OTHERWISE. THE COMMAND IS FETCHED AND IF 1040 ZERO IT MERNS THAT IT IS THE END OF THE SEQUENCE AND THE POINTER

1050 IS ALSO REINITIALIZED

| | | I860
1833- | R6 76 | LDX | 1070 | SADV LDX ♦SPNT | GET CONTROL SEQUENCE POINTER
1835- | Oft | DEX | 1088 | DEX | POINT TO NEXT SEQUENCE ENTRY
1836- | 10 02 | BPL | 1090 | BPL GSEQ | IF NOT TO END. BRANCH
1038- | ft2 07 | LDX | 1100 | SINT LDX 07 | RE-INIT SEQUENCE POINTER
103ft- | 86 76 | SIX | 1110 | GSEQ SIX *SPNT | SAVE SEQUENCE POINTER
1830- | 85 77 | LDfl | 1128 | LDfl *CSEQ.X | GET COMMAND FROM CONTROL SEO.
183E- | F0 F8 | BEQ | 1138 | BEQ SINT | ZERO ENDS THE SEQUENCE. BRANCH
| | | 1148
1158 ft NEW COMMAND FROM THE SEQUENCE. FIRST USE IT TO SET OR CLEAR THE
1160 | THE GLIDE CONTROL BIT FROM THE TRANSPOSE BUFFER. | IN THE PROCESS.
1170 THE NEW COMMAND IS SHIFTED ONE BIT TO THE LEFT; WHICH MULTIPLIES 1188 THE TEMPO VARIABLE BY 2 AND SHIFTS THE UP/DOWN AND LEGfl/STftCC BITS 1190 INTO MORE EASILY TESTED POSITIONS.
| | | 1200
1848- | 85 74 | STfi | 1210 | OLID STfi *SCTL | SAVE SEQUENCE ENTRY IN CONTROL BUFFER
1842- | 89 CO 00 | LDfl | 1220 | LDfl TTBL. V | GET THE CURRENT TRANSOSE BUFFER ENTRY
1845- | 2ft | ROL | 1230 | ROL | ROTATE GLIDE BIT TO CARRY
1046- | 06 74 | flSL | 1240 | ASL *SCTL | ROTATE CONTROL WORD GLIDE TO CARRY
1048- | 6ft | ROR | 1250 | ROR | ROTATE CARRY TO GLIDE BIT
1049- | 99 00 80 | STfl | 1260 | STfl TTBL. Y | THEN RETURN TO TRANSPOSE BUFFER
| | | 1270
1280 THIS LITTLE ROUTINE DETERMINES WHETHER SCAN IS UP OR DOWN AND 1290 INITIALIZES THE POINTER TO THE PROPER VALUE
1300 SKVP-SET KEY POINTER
| | | 1310
1040- | R2 07 | LDX | 1320 | SKYP LDX 07 | PREPARE FOR ARP. UP INITIAL POINTER
104k- | 24 74 | BIT | 1338 | BIT ♦SOIL | CHECK COMMAND BUFFER - ARP. UP?
1050- | 30 02 | BMI | 1348 | BMI STIM | YES. BRANCH
1852- | R2 00 | LDX | 1358 | LDX 08 | NO. ARP. DOWN INTIAL POINTER
| | | 1360
1378 NOW THE ROUTINE TO RESET THE TIMER. SINCE ALL KEY POINTER MANIPULATIONS 1388 WIND UP AT THIS POINT. THE FIRST INSTRUCTION IS TO SAVE THIS POINTER

1390 THE TIMER VALUE IS EXTRACTED FROM THE CONTROL WORD SOIL
1400 STIM-SET TIMER
| | | 1410
1054- | 86 73 | SIX | 1420 | SUM SIX *PNTR | SAVE INPUT BUFFER POINTER
1056- | R9 IF | LDfl | 1438 | LDfl IF | PREPARE MASK AND
1058- | 25 74 | AND | 1448 | AND *SCTL | GET THE TIMER (TEMPO) VALUE
185ft- | 85 72 | STfl | 1450 | STfl *TIMR | AND SAVE IN THE TIMER VARIABLE
| | | 1468
1470 NOW WE GET THE CURRENT NOTE OF INTEREST FROM THE INPUT BUFFER 1488 AND IF THE KEY IS NOT DOWN. A CHECK IS MADE TO SEE IF ANY KEYS
1498 | ARE DOWN. | IF NONE ARE. THE TIMER IS TRICKED INTO TIMING OUT THE
1508 NEXT TIME THROUGH WHICH WILL THEN RESULT IN THE WHOLE COMMAND

1510 SEQUENCE FOLLOWING SYSTEM BEING RESET
| | | 1528
1050- | 85 E0 | LDfl | 1538 | LDfl *KTBL. X | GET THE CURRENT KEY FROM INPUT BUFFER
105E- | D0 00 | BNE | 1548 | BNE BOUT | IF ZERO. NO KEY - BRANCH
1068- | 24 E7 | BIT | 1558 | BIT *KTBL+07 | ARE ANY KEYS DOWN?
1062- | 70 BF | BVS | 1568 | BVS ADVA | YES. BRANCH
1064- | R9 81 | LDfl | 1570 | LDfl 81 | NO. PREPARE TO MAKE TIMER RUN OUT
1866- | 85 72 | STfl | 1588 | STfi *TIMR | NEXT PASS THROUGH
1068- | 89 V8 88 | LDfl | 1598 | CLRN LDfl NTBL. V | GET THE CURRENT OUTPUT NOTE
1068- | 29 BF | AND | 1608 | AND 0BF | CLEAR THE TRIGGER FLAG
106D- | 99 08 88 | STfi | 1610 | BOUT STR NTBL-Y | AND REPLACE IN OUTPUT BUFFER
1078- | 68 | RTS | 1628 | RTS | RETURN
| | | 1630

### November/December 1979

1640
1650

NOW SOME TEMPORARY LOCATIONS ffl® THEIR INITIAL STATES

1071 | 00 | 1660 | TEMP . HS 00
1072 | 01 | 1670 | TIMR . HS 01
1073 | 08 | 1680 | PNTR . HS 08
1074 | C4 | 1690 | SCTL . HS C4
1075 | 07 | 1700 | 5PNT . HS 07
1076 | 07 | 1710 | SPNT . HS 07
1077 | 000000 | 1720 | bEU | Hb 00MU00U000WkiE404
1740 .OR 10E8
1750 5TUP . HS 482004
1770 . OR 1100
1790 THIS IS THE COMMAND KEY DECODING BND SEQUENCE EDITING SUBROUTINE
1800 | # OF COMMRt© KEY | S IN Y REGISTER
1810
1100- | 86 75 | LDX | 1820 | CMND LDX *PPNT | GET THE EDITORS POINTER TO COMMAND SEQ
1102- | 85 77 | LD8 | 1830 | | LDR *CSEQ, X | GET THE COMMAND POINTED TO (IN BCC, DON'T FORGET)
1104- | C0 10 | CPY | 1840 | | CPY 10 | IS KEY 10 - CLEAR COMMAND SEQUENCE
1106- | F0 0F | BEQ | 1850 | | BEQ CLR | YES, BRANCH
1108- | 30 IF | BCC | I860 | | BCC CNXT | NO, IT'S LESS THAN °F", BRANCH
| | | 1870
1889 | THE KEY IS 11 OR GREfiTER. | EXCHfiNGE THE COMMRND POINTED TO WITH
1890 TEMPORARY STORAGE LOCATION TEMP. NOTE THAT THIS CAN BE USED TO 1900 EXCHANGE TWO OR MORE COMMANDS IN THE SEQUENCE
| | | 1910
1108- | 84 71 | LDY | 1928 | | LDY *TEMP | GET THE COMMAND IN THE TEMPORARY BUFFER
110C- | D0 04 | BNE | 1930 | | BNE ELP0 | IS THE COMMAND FROM TEMP A 0? NO, BRANCH
110E- | E0 87 | CPX | 1940 | | CPX 07 | POINTING TO FIRST COMMAND?
1110- | F0 28 | BEQ | 1950 | | BEQ RTN | YES, BRANCH. DON'T WRITE ZERO AS FIRST COMMAt©
1112- | 94 77 | STY | i960 | ELP0 STY *CSEQ,X | PUT COMMRND IN THE SEQUENCE SLOT POINTED TO
1114- | 85 71 | STB | 1970 | | STR *TEMP | fit© THEN SAVE OLD COMMAND IN THE TEMP LOCATION
1116- | 60 | RTS | 1980 | | RTS | THEN RETURN
| | | 1990
2000 THE KEY IS "10% CLEAR THE COMMAND SEQUENCE. NOTE THAT THE FIRST 2010 ENTRY IN THE SEQUENCE IS NOT CHANGED.
| | | 2020
1117- | 82 07 | LDX | 2030 | CLR | LDX 07 | SET POINT TO FIRST SEQUENCE ENTRY
1119- | 86 75 | SIX | 2040 | | SIX +PPNT | AND SAVE IT
1118- | C8 | DEX | 2050 | | DEX | DECREMENT THE POINTER(SKIP FIRST ENTRY)
111C- | 89 00 | LDB | 2060 | | LDR 00 | AND GET READY
111E- | 8V 20 18 | STR | 2070 | | STR DISP | ZERO THE DISPLAYED EDITOR POINTER
1121- | 85 71 | STR | 2080 | | STB *TEMP | AND THE EXCHANGE REGISTER
1123- | 95 77 | STR | 2090 | CLLP STR *CSEQ, X | ZERO THE SEQUENCE ENTRY
1125- | C8 | DEX | 2100 | | DEX | AND POINT TO NEXT ENTRY
1126- | 10 FB | 8PL | 2110 | | BPL CLLP | SOME LEFT, LOOP
1128- | 68 | RTS | 2120 | | RTS | RETURN
| | | 2138
2140 NOW WE TEST FOR " " OR "F“, BACKSPACE OR ADVANCE THE EDITOR'S
2150 EDITOR'S POINTER TO THE C0MBNV SEQUENCE. NOTE THAT INCREMENTING THE 2160 POINTER PRODUCES R BACKSPACE.
| | | 2170
1129- | C0 0E | CPY | 2180 | CNXT CPY 0E | IS KEY "E" OR "F"?
1128- | 90 18 | BCC | 2190 | | BCC SIMP | NEITHER AND LESS THAN "E“, BRANCH FOR NEXT TEST
1120- | F0 0F | BEQ | 2200 | | BEQ BACK | IT'S "E", BRANCH TO BACKSPACE
112F- | ca | DEX | 2210 | | DEX | IT'S "F", ADVANCE THE POINTER
1130- | 30 08 | BNI | 2220 | | BMI RTN | AND IF OUT OF RANGE, BRANCH TO LEAVE IMMEDIATELY
1132- | 86 75 | SIX | 2230 | COM SIX *PPNT | SAVE NEW POINTER
| | | 2240
2250 IN THIS SECTION THE POINTER (miCH IS 07 FOR THE START OF Tt£ SEQUENCE 2260 AND 00 RT THE END) IS CONVERTED TO RN INCREASING NUMBER FROM 0-7 FOR 2270 DISPLAY PURPOSES.
| | | 2280
1134- | 88 | TXR | 2290 | | TXR | POINTER TO THE ACCUM. FOR A CALCULATION
1135- | 38 | SEC | 2380 | | SEC | PREPARE FOR A SUBTRACTION
1136- | E9 08 | SBC | 2310 | | SBC 08 | TWO'SD COMPLEMENT
1138- | 49 FF | EOR | 2320 | | EOR 0FF | COMPLEMENT OF THAT
1138- | 8V 20 18 | STR | 2330 | | STR DISP | SHOW VALUE IN THE DISPLAYS
113V- | 60 | RTS | 2340 | RTN | RTS | RETURN
| | | 2350
2360 BBCKSPRCE POINTER AND MAKE SURE IT IS STILL IN RANGE, THEN BRANCH
| | | 2370
113E- | E8 | INX | 2380 | ACK INX | BACKSPACE THE POINTER
1135- | E0 08 | CPX | 2398 | | CPX 08 | OUT OF RANGE?
1141- | F0 FA | BEQ | 2400 | | BEQ RTN | YES, BRANCH TO LEAVE IMMEDIATELY
1143- | V0 ED | BNE | 2410 | | BNE COUT | NO, BRANCH ALWAYS TO SAVE POINTER, ETC.
| | | 2420
2430 IF THE KEY IS ONE OF THE TEMPOS, ADD 1 (0 TEMPO NOT ALLOWED) RND 2440 FIT IT INTO THE CONTROL SEQUENCE ENTRY POINTED TO
| | | 2450
1145- | C0 08 | CPY | 2460 | STMP CPY 08 | TEMPO KEY?
1147- | 80 08 | BCS | 2470 | | BCS SGLD | NO, BRANCH
1149- | C8 | INY | 2480 | | INY | YES, ADD 1 TO KEY #
1148- | 29 F0 | RND | 2490 | | At© 0F0 | MASK PRESENT TEMPO IN COMMAND TO ZERO
114C- | 95 77 | STR | 2500 | | STR *CSEQj X | SAVE CONTROL FLAGS IN CSEQ TEMPORARILY
H4E- | 98 | TV8 | 2510 | | TYR | BRING NEW TEMPO TO ACC

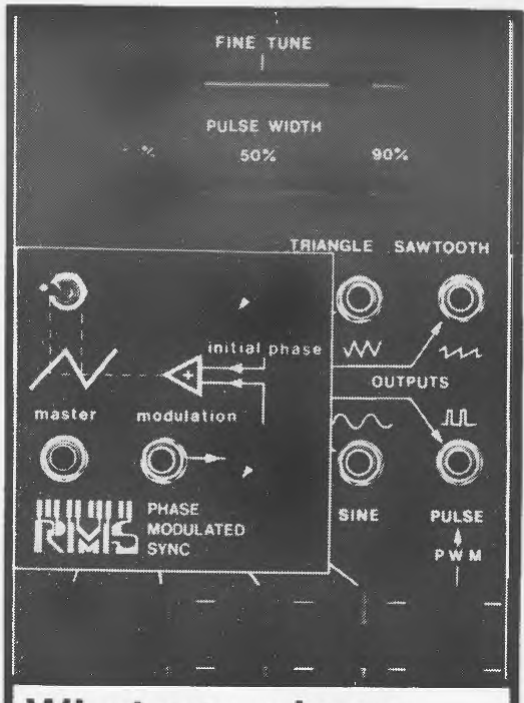
[picture p25: figure]

# What can phase-modulated sync do for your 2600 ?

For a detailed explanation of phase-modulated sync and our other modifi-cations (like voltage-controlled Q and a comparator) for your 2600, write to Rivera Music Services.
48 Brighton Ave. #11.
Boston. Mass. 02134.
or call us at
617-782-6554. | ML Rivera
| Services

# Advertiser Index

Aries Music | 35
Blacet Music Research | 4, 28
Dickstein Distributors | 34
Godbout Electronics | 4
Harris Music Company Ltd | 13
Paia Electronics | 29, 36
PolyMart | 18-19
Polyphony Back Issues | 20
Pratt Read Keyboards | 17
Rivera Music Services | 23, 33
Serge Modular Music | 7
Speaker Builder Magazine | 11
Southwest Tech Products | 2
Synergetics | 31
When you | write | or order from | our
advertisers, | be sure | to tell them
that | you | saw | their | products | in

# pouPHOhiy

FWPHONU | November/December 1979 | 33

2860 :

2879 | END | EN
1145- | 15 77 | ORA | 2520 | 0R8 *CSEQ,X | COMBINE WITH OLD CONTROL FLAGS
1151- | D0 1A | BNE | 2530 | BNE SAVA | BRANCH ALWAYS
| | | 2540
2550 NOH A SERIES OF TESTS WHICH RESULT IN THE OARRV BIT BEING SET OR 2560 CLEAR. A SERIES OF ROTATES BRINGS THE OARRV TO THE APPROPRIATE BIT 2570 IN THE COMMAND HORD
| | | 2588
1153- | 28 | ROL | 2590 | SOLD ROL | ROTATE THE GLIDE COMMAND BIT TO CARRY
1154- | 08 | PHP | 2600 | PHP | AND SAVE THE CARRY ON THE STACK
1155- | 00 09 | OPV | 2610 | OPV 09 | IS KEV GLIDE ON OR OFF?
1157- | 50 12 | BEQ | 2620 | BEQ ROTI | 9-GLIDE ON, BRANCH
1159- | 90 10 | 800 | 2630 | BOO ROTI | 8-GLIDE OFF, BRANCH
| | | 2640
2650 THE KEV HAS NEITHER GLIDE ON NOR OFF, TEST FOR DIRECTION UP OR DOOUN
| | | 2660
1158- | 28 | PLP | 2678 | SHOD PLP | GET THE OLD GLIDE BIT FROM THE STACK
1150- | 28 | ROL | 2680 | ROL | ROTATE DIRECTION BIT TO CARRY
115D- | 08 | PHP | 2690 | PHP | SAVE IT ON STACK
1155- | 00 08 | OPV | 2700 | OPV 08 | IS KEV UP OR DOWN?
1160- | 50 08 | BEQ | 2710 | BEQ R0T2 | B-UP, BRANCH
1162- | 90 06 | 800 | 2720 | BOO R0T2 | A-DOHN, BRANCH
| | | 2730
2740 THE KEV HAS TO BE C OR D (STACCATO OR LEGATO)
| | | 2750
1164- | 28 | PLP | 2760 | SDIR PLP | GET THE OLD DIRECTION BIT
1165- | 28 | ROL | 2770 | ROL | STAC/LEGA BIT TO CARRY
1166- | 08 | PHP | 2780 | PHP | SAVE IT
1167- | 00 00 | OPV | 2790 | OPV 00 | CARRY SETS IF KEY IS "D" - LEGATO
1169- | 68 | ROR | 2800 | ROR | ROTATE COMMAND HORD BACK INTO PLACE
1168- | 68 | ROR | 2810 | R0T2 ROR
1168- | 68 | ROR | 2820 | ROTI ROR
1160- | 28 | PLP | 2830 | PLP | HASTE A STACK SLOT TO COMPENSATE
1160- | 95 77 | STB | 2840 | SAVA STS *CSEQ,X | SAVE THE COMMAND HORD IN THE SEQUENCE
1165- | 60 | RTS | 2850 | RTS | RETURN

# 'EQUIPMENT’

# iExcrawg®:

List | equipment | or | services | for sale,
trade, or | wanted, | plus | job | openings,
positions wanted, events and so on. Keep
listings | brief; | enclose $1.00 for each
10 words. Prices, zip, and phone numbers
count as a | single | word | each. | Display
classifieds are available for commercial
ads; | rates | are | $10 | per | column | inch
(minimum, | negative | supplied). | Respond
directly to the advertiser. Please don't
write | to | POLYPHONY. | Polyphony | is not
responsible for claims made in | ads, | or
the | results | of | any | transactions. | We
reserve the right to edit or refuse | any
ads submitted.
DISTORTION | ANALYZERS | HP330B (harmonic)
$130; Heathkit | IM-22 | (intermodulation)
$65; | AN/USM-140D | 22MHz scope with dual
trace and delayed | sweep | (Lavoie | Labs)
$575; | Scott *335 multiplex adapter $25;
EMC model 801 C & R bridge $25; Citation
V amplifier $50. | Plus | shipping. | Ralph
Ehat, | 124 | Barcelona St., Camarillo, CA
93010, Ph. 805-484-1454.

# BY PROFESSIONAL DEMAND

DDC OFFERS FREE ADVICE, PERSONAL SERVICE AND ONE-DAY SHIPPING OF THE FINEST MUSIC AND SOUND EQUIPMENT AVAILABLE ANYWHERE:

# MNER

# multivox

KaseY/SMF

# NovaLine

# intersound

## Oberlwhn

VW

# © croujn

# pol^ypusfon

## ^EOUcDmAL CRCUitJ

•NIYK.

# KOBE

MUTRON

PLEASE CALL OR WRITE FOR PR ICES & ORDERING INFORMATION - YOU'LL BE GLAD YOU DID!

DDC DICKSTEIN | DISTRIBUTING | COMPANY
1120 QUINCY PPY—SCRANTON, PA 18510 PHONE ORDERS WELCOME: (717) 344 7469

2720R KEYBOARD Very good condition, can be used separately or to complement your present system. $350 or best offer. Andy
Eddy, RED #1, | Winsted, | CT | 06098, | Ph.
203-379-6217. Must sell.
ARIES | MODULES: | (2) | AR-317 VCOs @ $182
each, (2) AR-312 Envelope | Generators | @
$110 | each, (2) AR-316 VCAs @ $121 each,
and one AR-327 multi-mode | VCF | @ | $248.
Rivera Music Services, 48 Brighton Ave. #11, Boston, MA 02134, (617) 782-6554.
WANT TO CORRESPOND with anyone | who | has
used | microcomputers | to | customize
non-Paia | monotonic | synthesizers | to
polyphonic. | Ron | Rockwell, | 25 Pleasant
St., Bethel, CT 06801
PAIA MODULES: 8700 Computer | with | PS-87
and | CS-87, | D/A | with | Quash, | (3) 4720
VCOs, | 4730 | VCF, | (2) | 4710 | Balanced
Modular/ | VCAs, (2) Envelope Generators,
4711 Stereo Mixer, Reverb | unit, | 2720-5
LFO/ | Noise, | 8782 | Keyboard, | (3) | Watt
Blocks. | All | assembled, | cabinets
available. | Guy Kilpatrick, 510 College.
Apt #416, Grand Rapids, MI 49503, | (616)
451-0578.
PAIA | 4700/S | with | Envelope | Follower,
$500. Oz, | $85. | Gnome, | $50. | Phianger,
$60. | All | fully | assembled and working.
Dave Mason, 2222 Harriman | Ln., | Redondo
Beach, CA 90278, (213) 379-5601.
DIGITAL | GROUP | Z80 | computer, | 10K RAM,
video | and | cassette | interface, | four
parallel | I/Os, 12 A power supply, ASCII
keyboard, documentation. | $750 | or | best
offer. Marvin Jones, Box 20305, Oklahoma City, OK 73156.
34 | POUJPHONU | November/December 1979
